P4V77/DiplomaThesis/LaTeX/kapitola2/figures/block_diagram.pdf

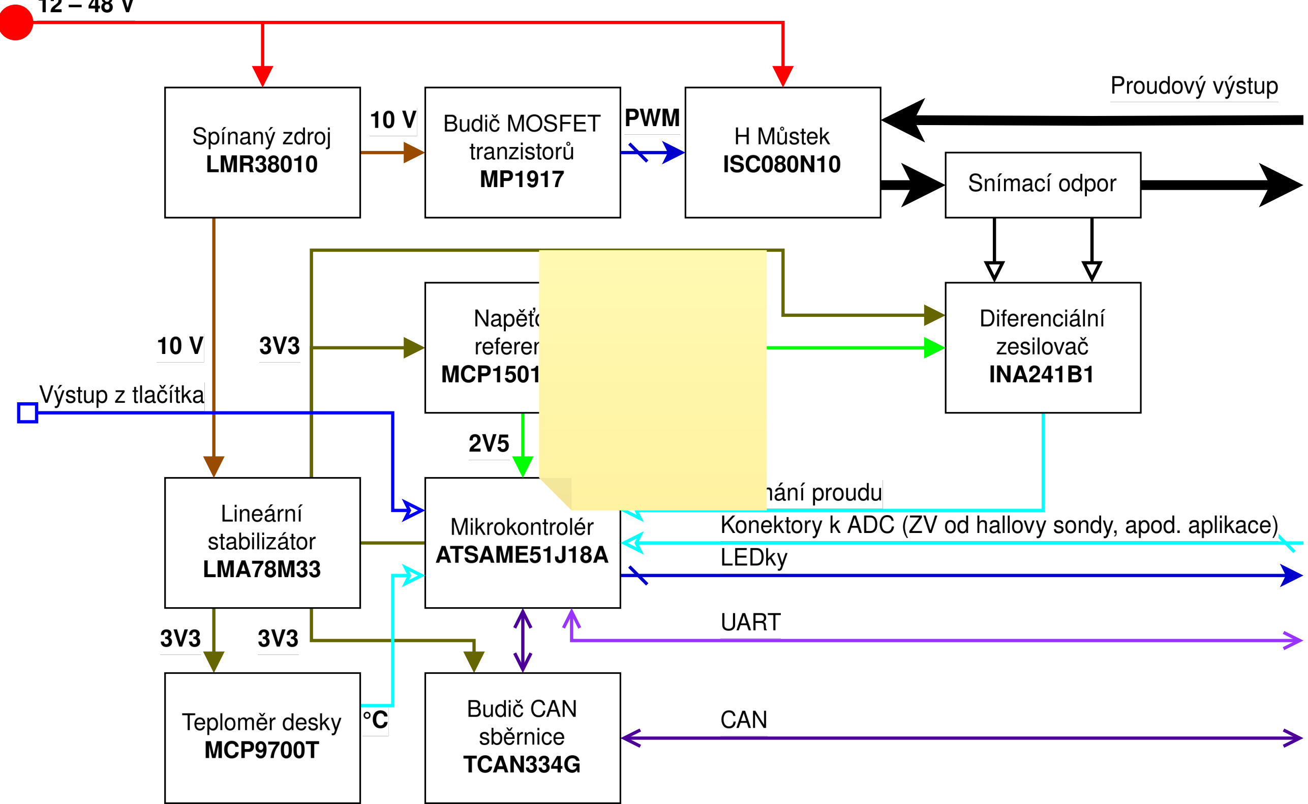
[picture p20: figure]
