P4V77/DiplomaThesis/LaTeX/kapitola2/figures/can_connector.pdf

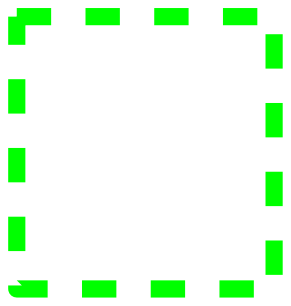
[picture p21: page 1]
