P4V77/DiplomaThesis/LaTeX/kapitola3/figures/boxes_back.pdf

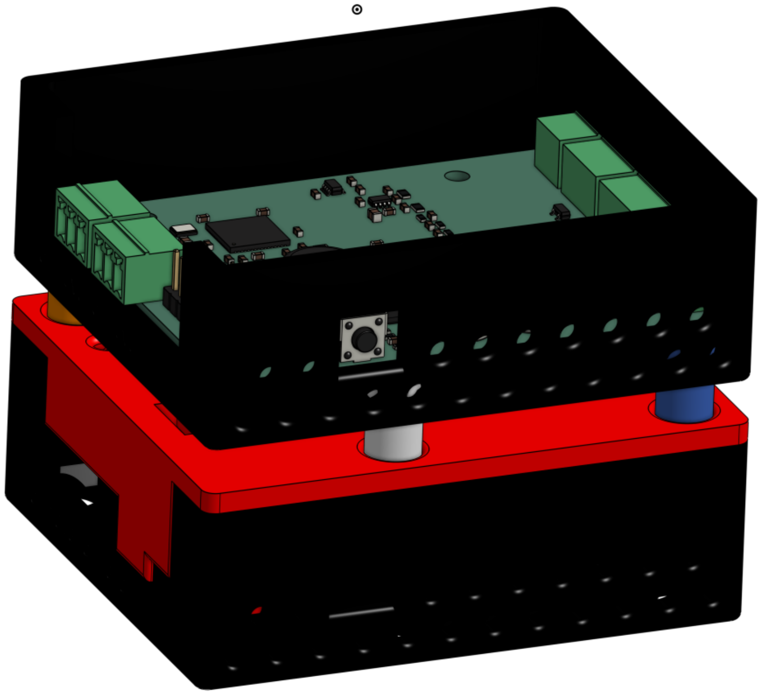
[picture p22: page 1]
