P4V77/DiplomaThesis/LaTeX/kapitola3/figures/boxes_front.pdf

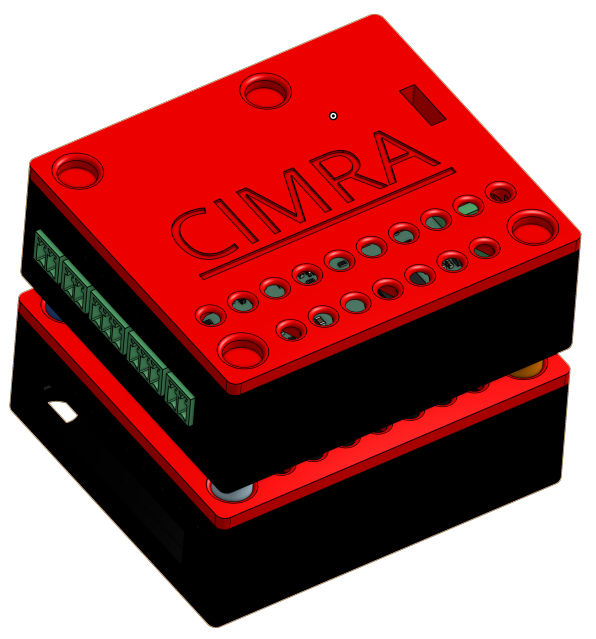
[picture p23: page 1]
