P4V77/DiplomaThesis/LaTeX/kapitola3/figures/pap_holder.pdf

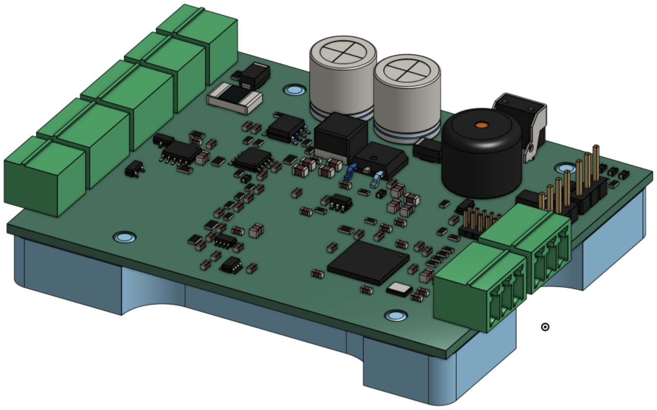
[picture p24: page 1]
