P4V77/DiplomaThesis/LaTeX/kapitola4/figures/flowchart_regulator_current.pdf

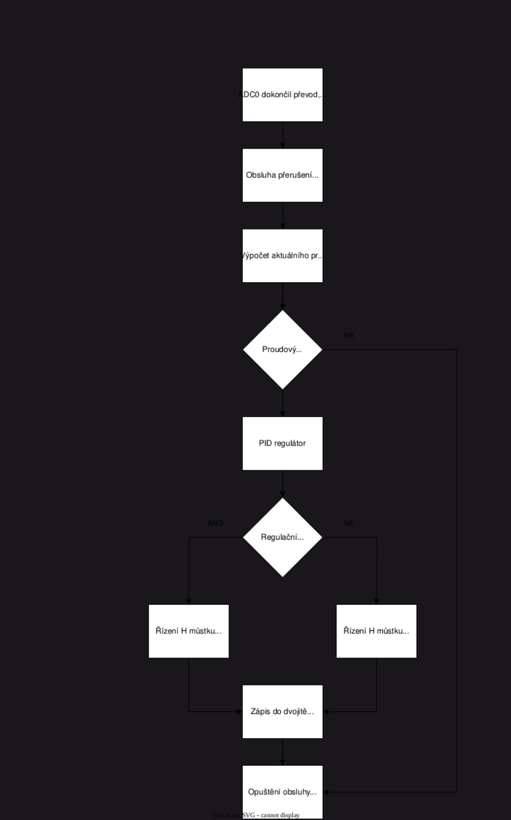
[picture p25: page 1]
