P4V77/DiplomaThesis/HW/Loga/cimra.png

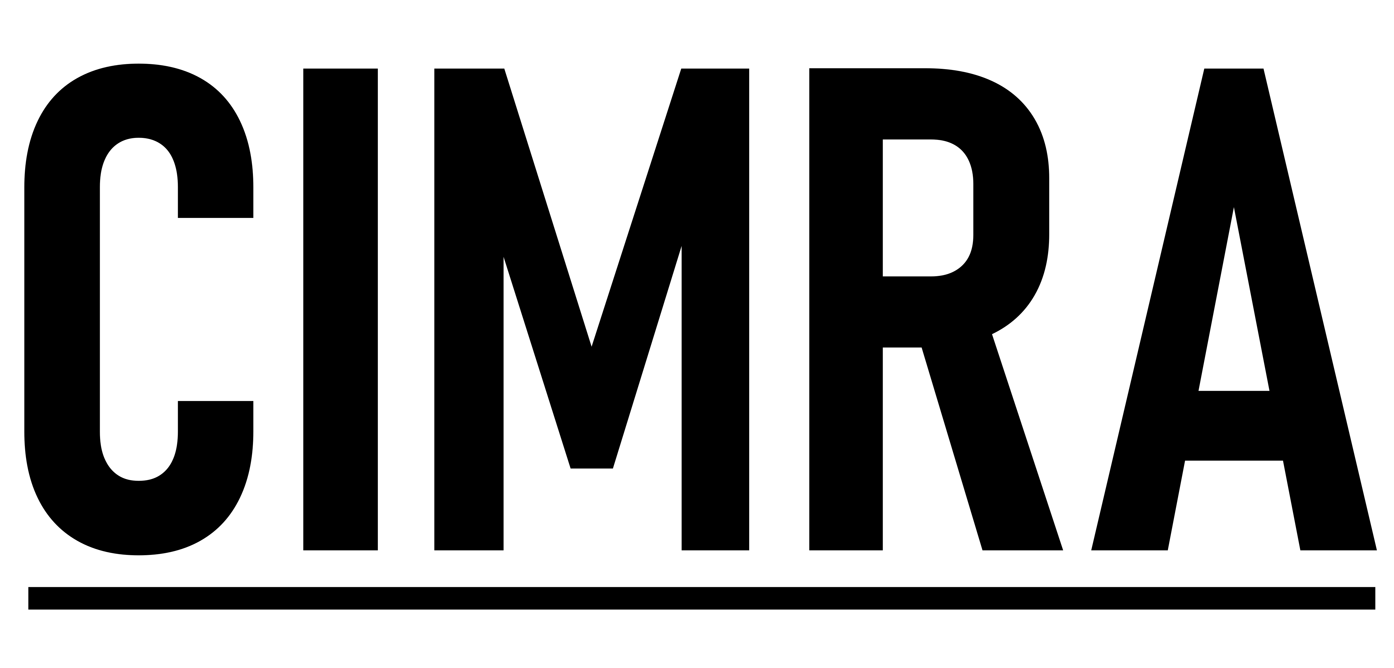
HW/Loga/cimra.png
