P4V77/DiplomaThesis/HW/Loga/ZCU.png

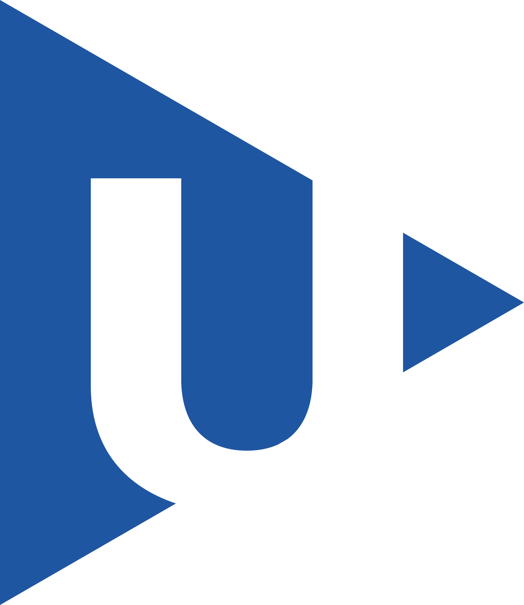
HW/Loga/ZCU.png
