P4V77/DiplomaThesis/LaTeX/kapitola5/Figures/Analyza_THD.png

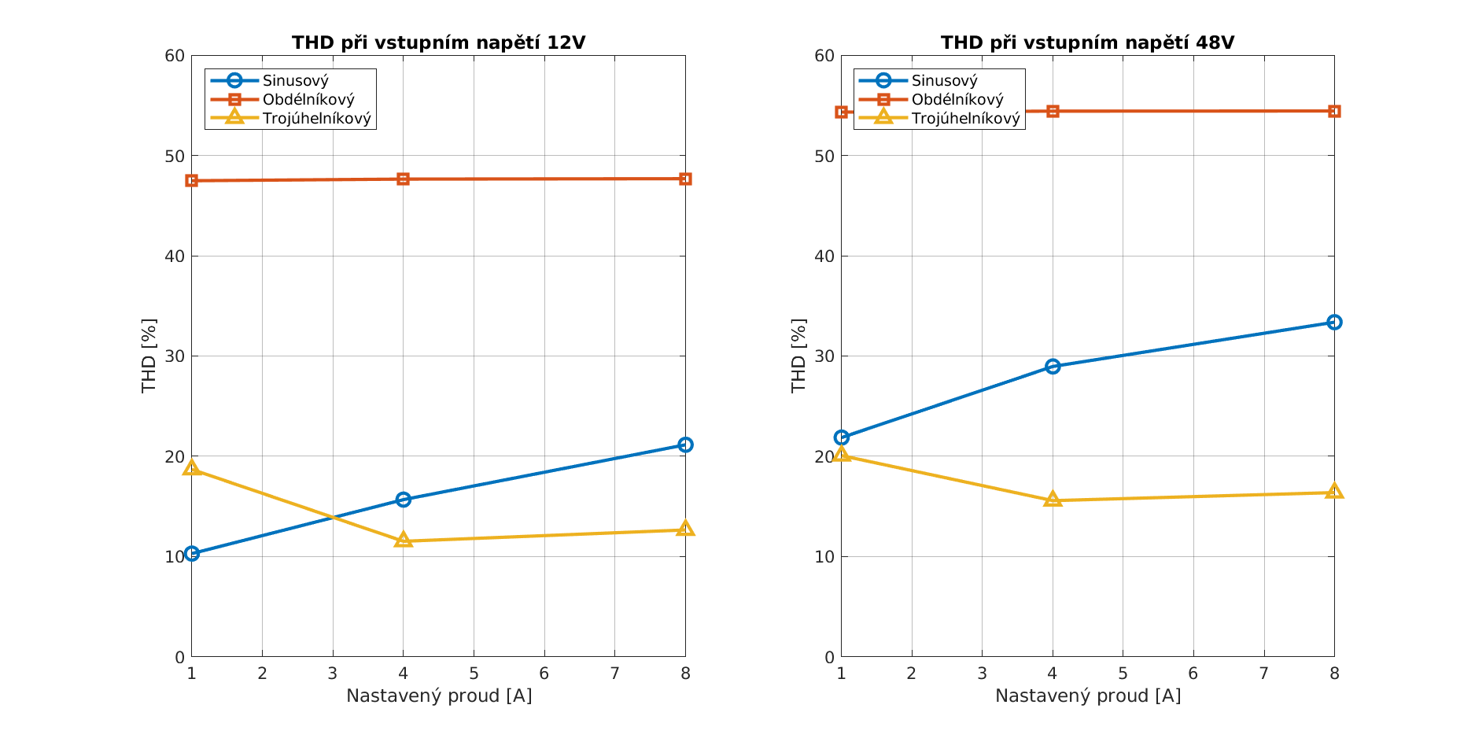
LaTeX/kapitola5/Figures/Analyza_THD.png
