P4V77/DiplomaThesis/LaTeX/kapitola5/Figures/Analyza_zakladni_harmonicke.png

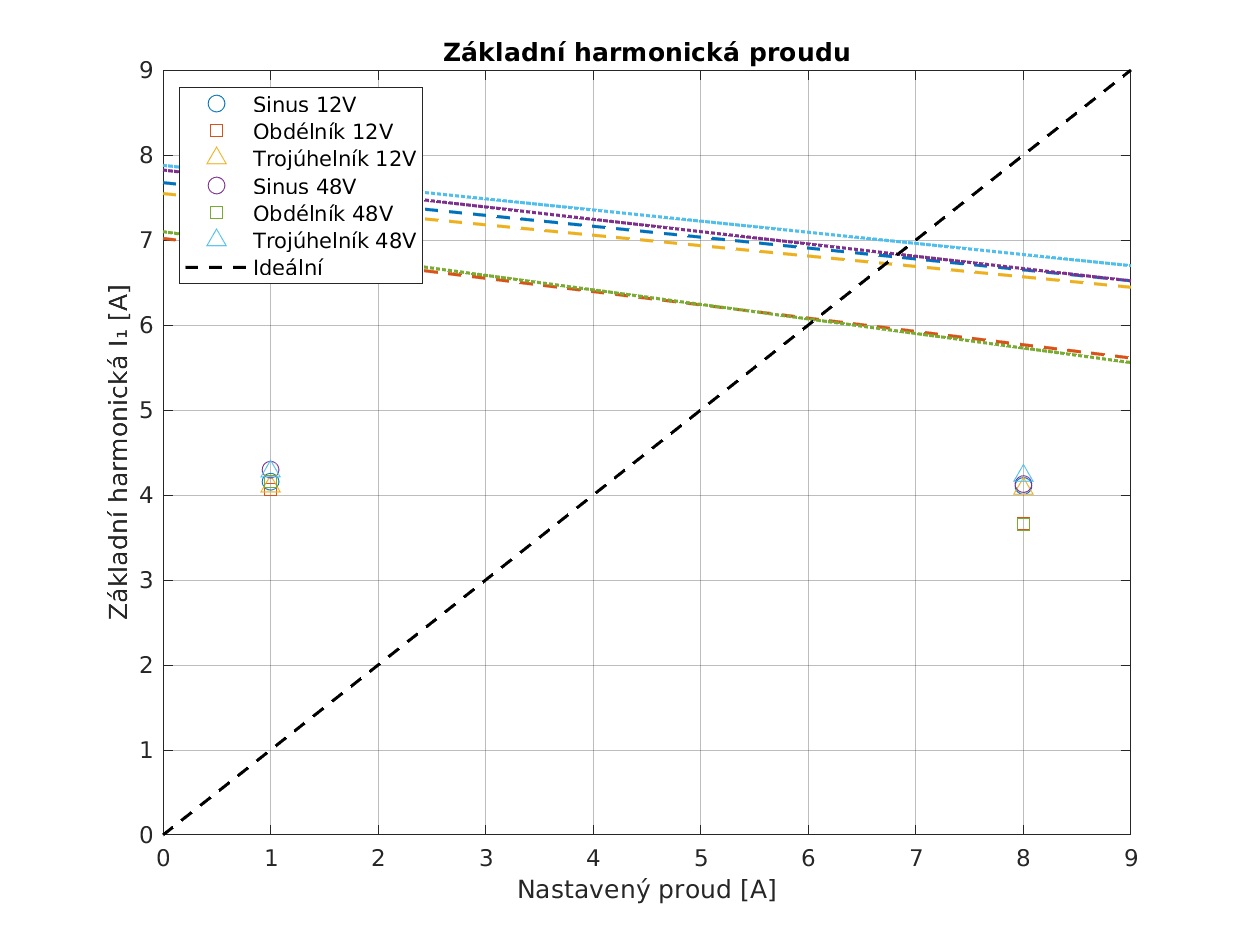
LaTeX/kapitola5/Figures/Analyza_zakladni_harmonicke.png
