P4V77/DiplomaThesis/LaTeX/kapitola5/Figures/Analyza_zakladni_harmonicke_smooth.png

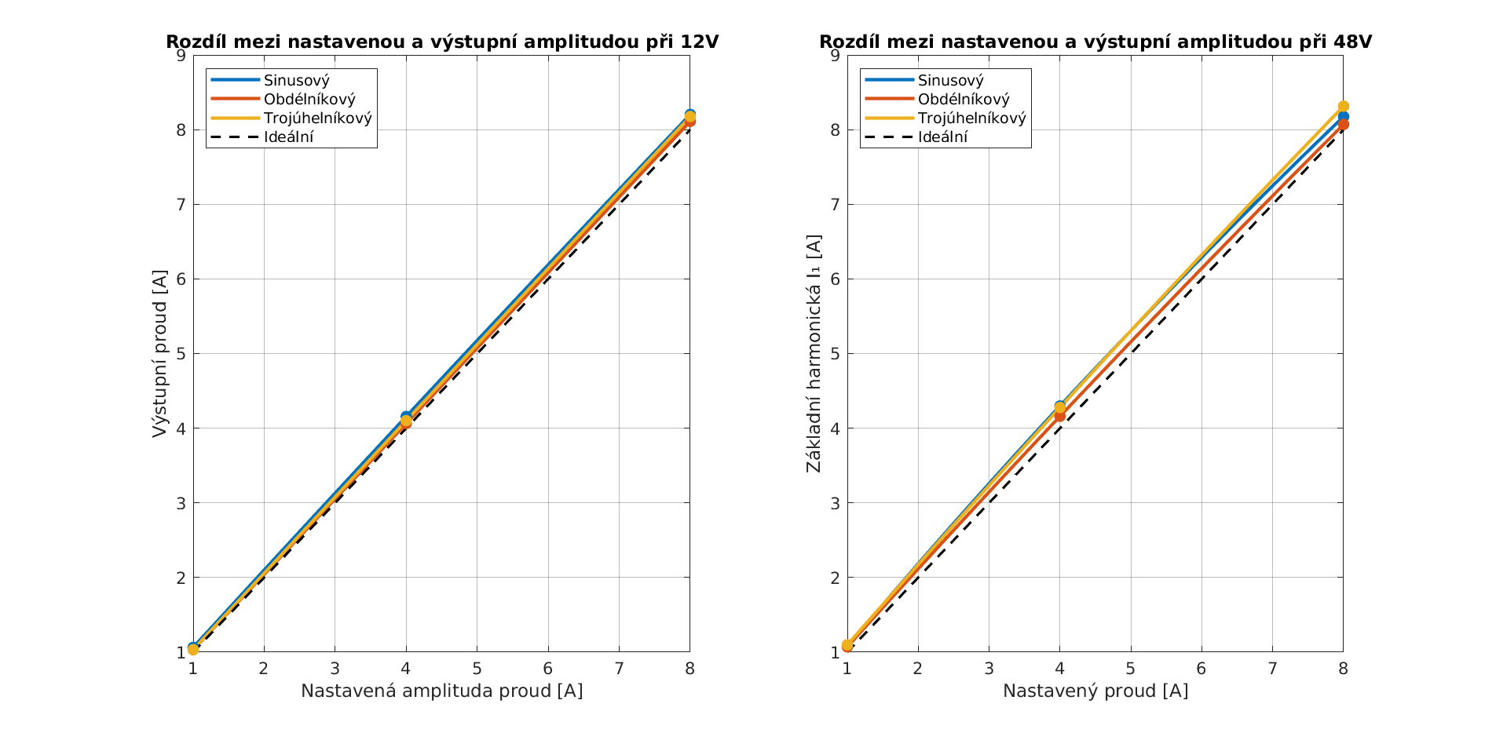
LaTeX/kapitola5/Figures/Analyza_zakladni_harmonicke_smooth.png
