P4V77/DiplomaThesis/LaTeX/kapitola5/Figures/DC_IRMS.png

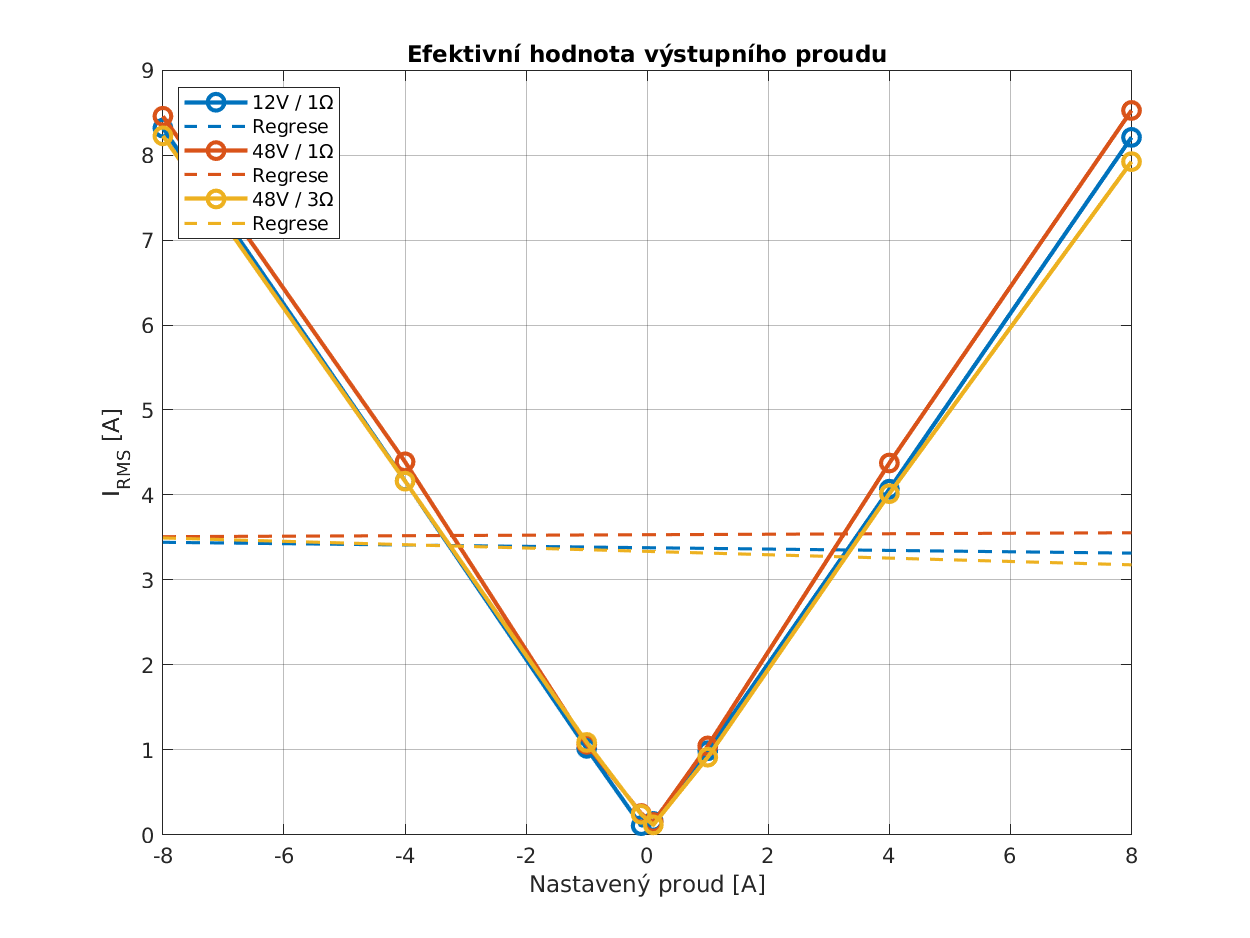
LaTeX/kapitola5/Figures/DC_IRMS.png
