P4V77/DiplomaThesis/LaTeX/kapitola5/Figures/DC_ucinnost_31V.png

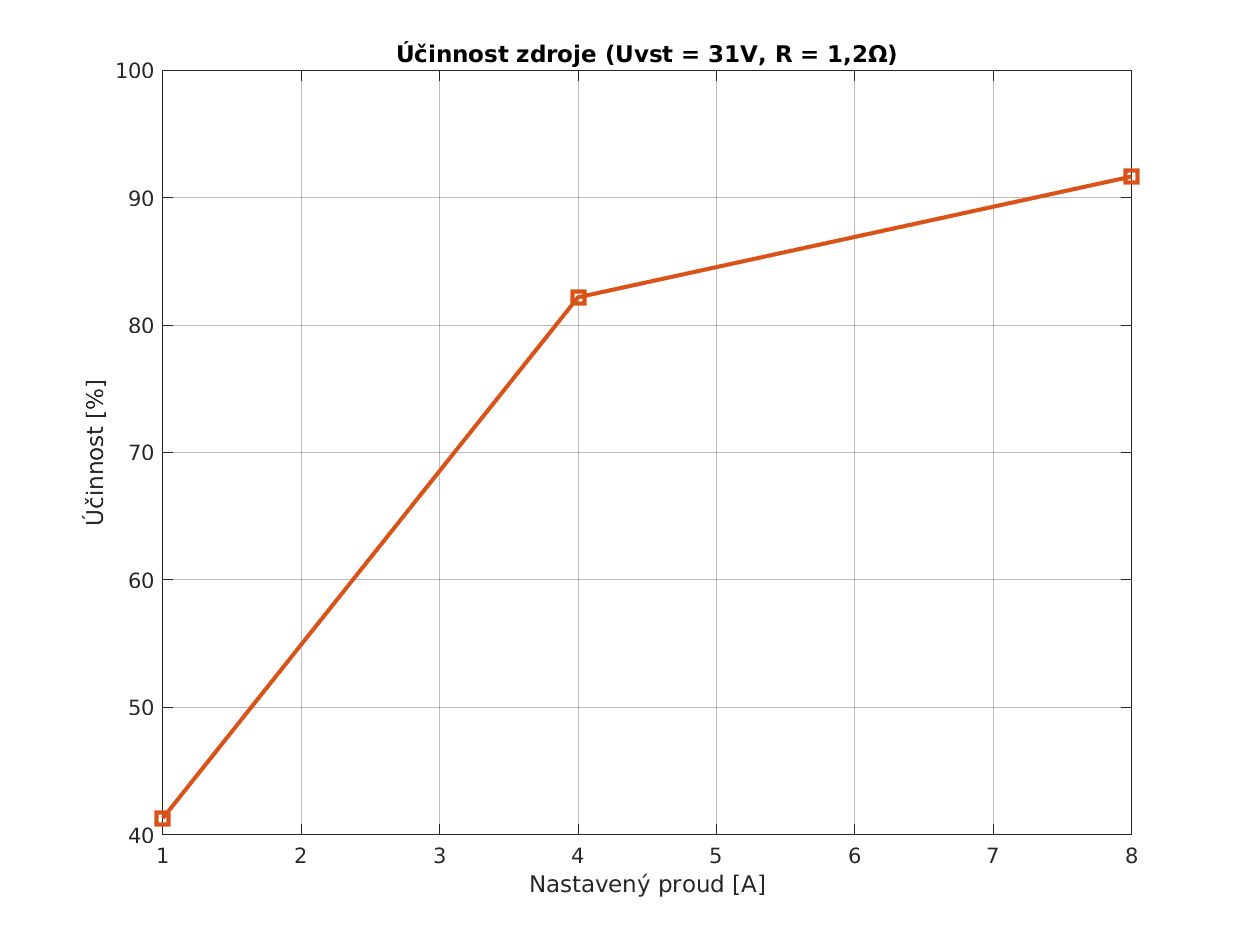
LaTeX/kapitola5/Figures/DC_ucinnost_31V.png
