P4V77/DiplomaThesis/LaTeX/kapitola5/Figures/DC_zvlneni_pp.png

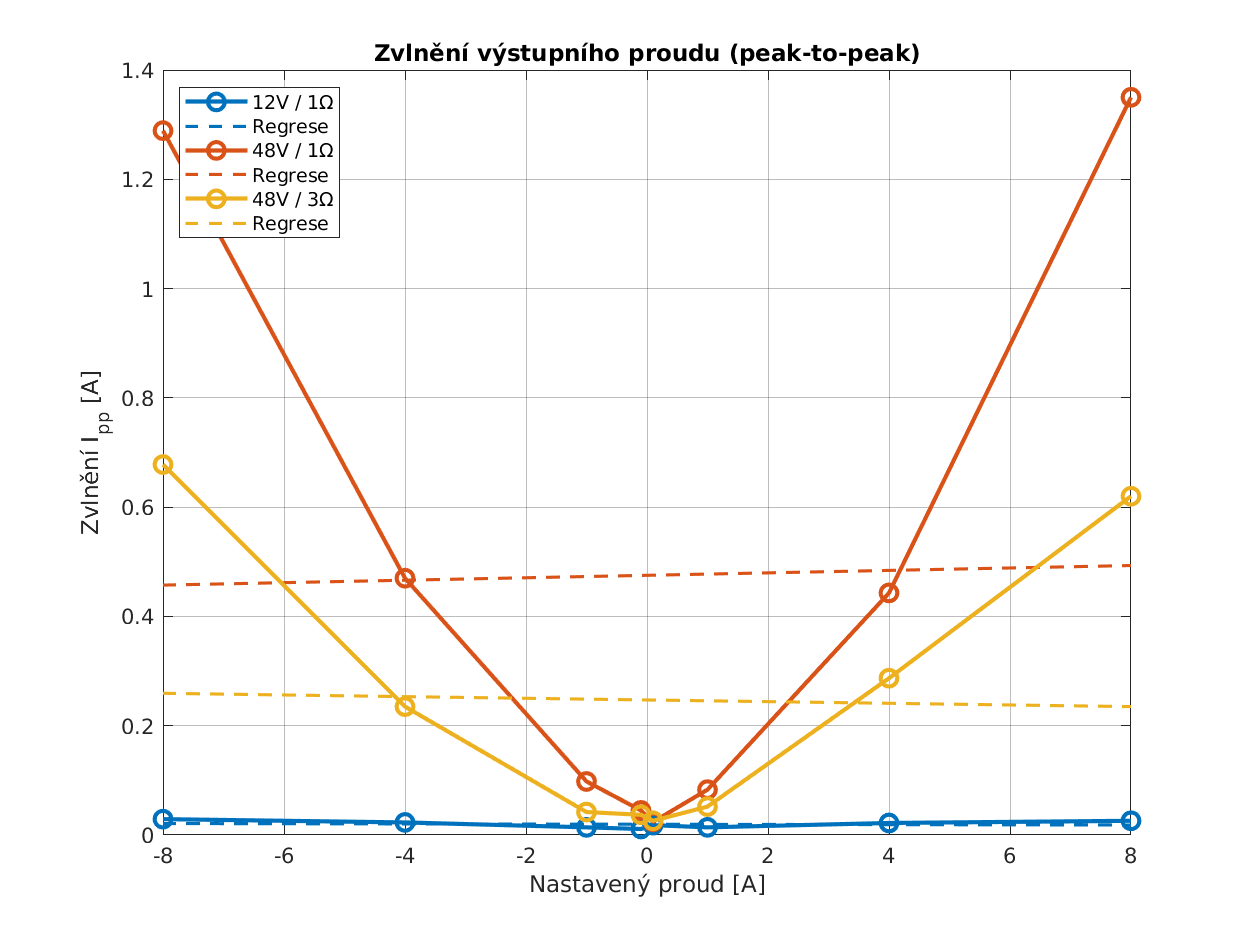
LaTeX/kapitola5/Figures/DC_zvlneni_pp.png
