P4V77/DiplomaThesis/LaTeX/kapitola5/Figures/Fundamental_Current.png

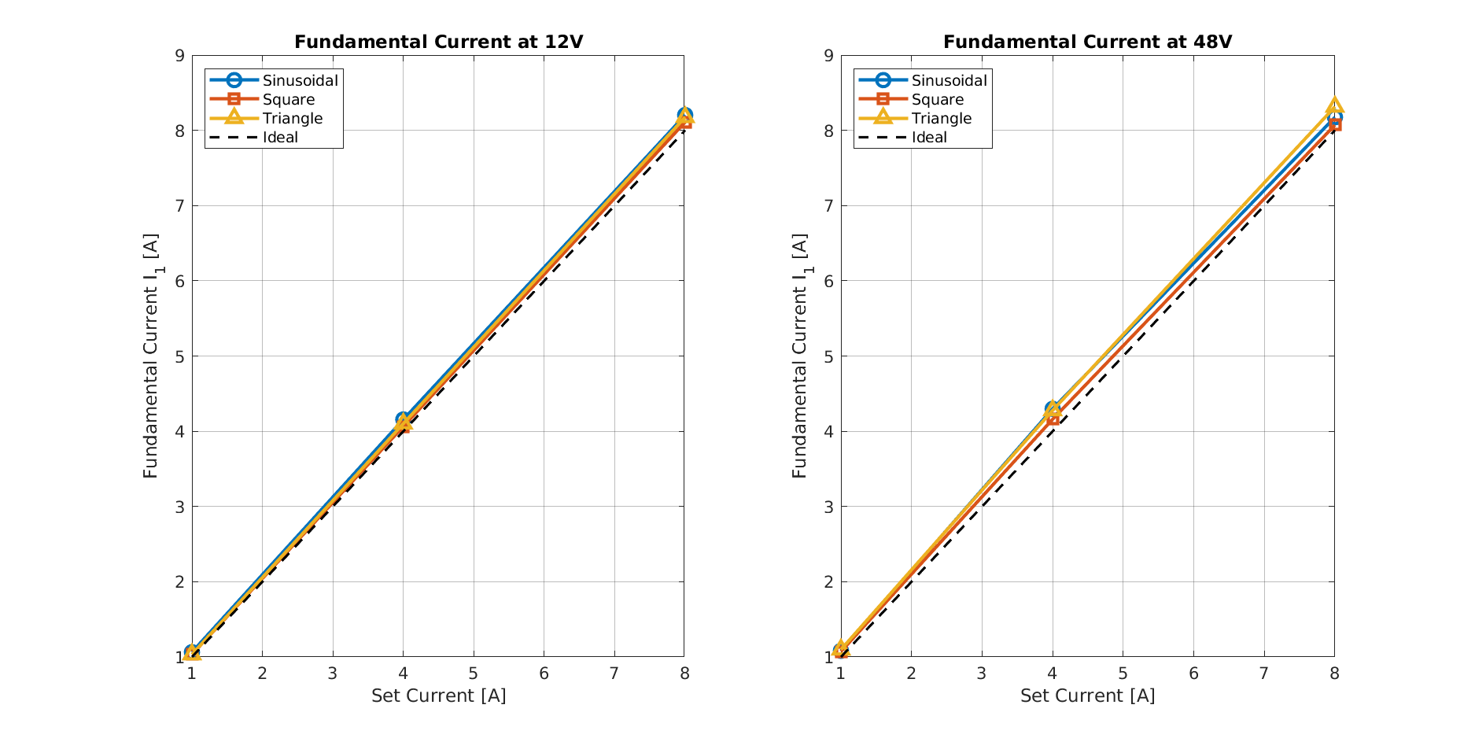
LaTeX/kapitola5/Figures/Fundamental_Current.png
