P4V77/DiplomaThesis/LaTeX/kapitola5/Figures/Graf4_Zatezova_char_napeti.png

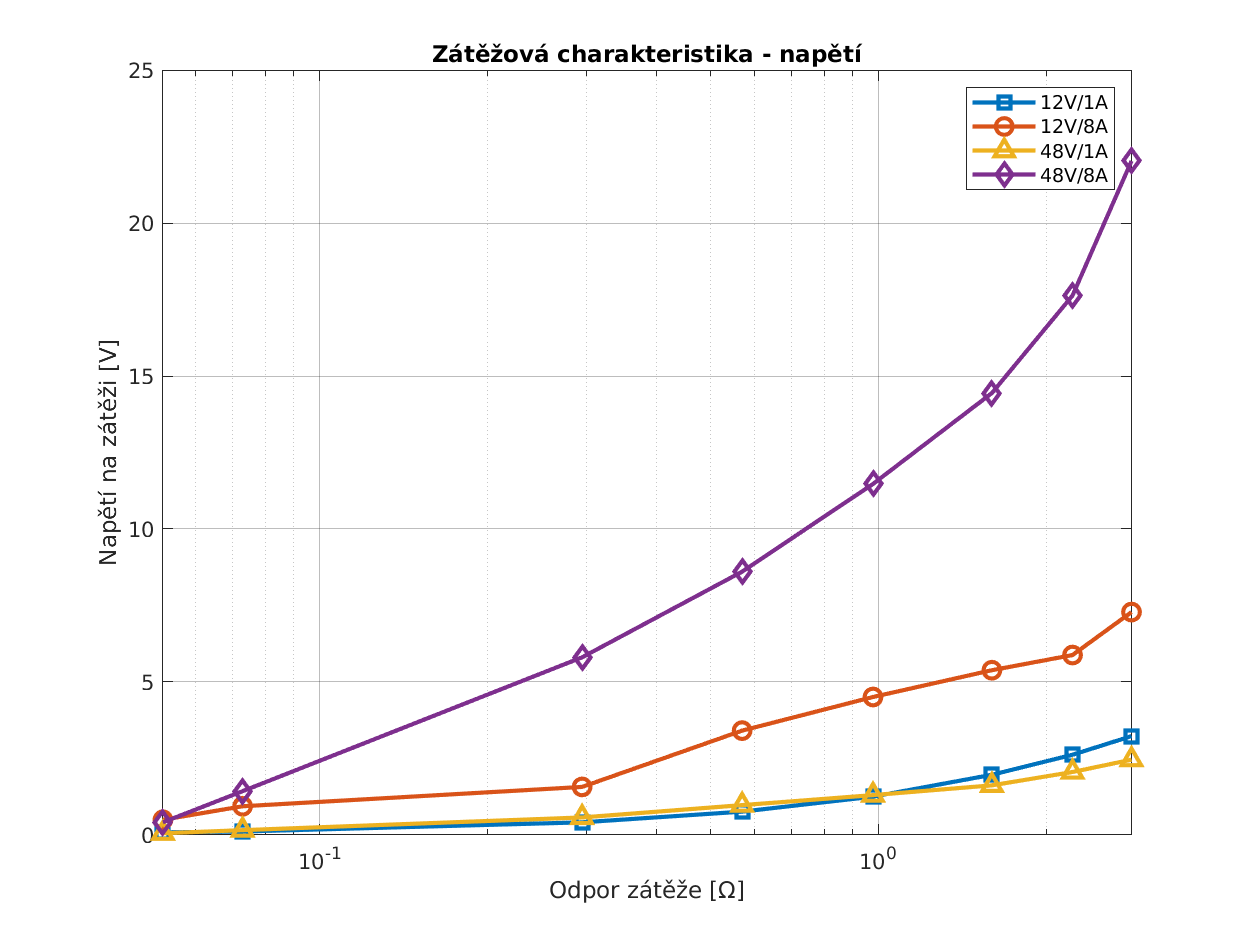
LaTeX/kapitola5/Figures/Graf4_Zatezova_char_napeti.png
