P4V77/DiplomaThesis/LaTeX/kapitola5/Figures/THD_kombinovane.png

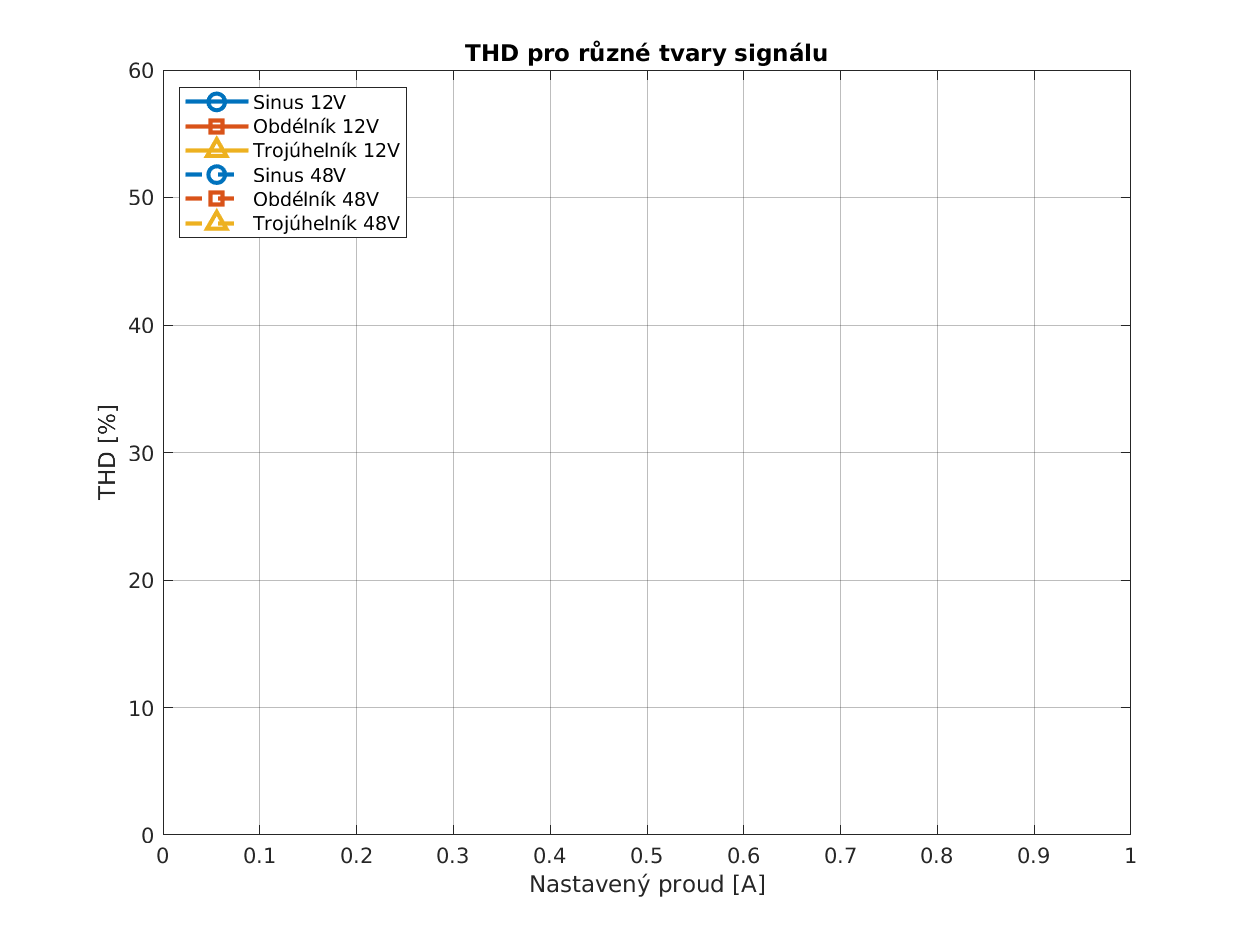
LaTeX/kapitola5/Figures/THD_kombinovane.png
