P4V77/DiplomaThesis/LaTeX/kapitola5/Figures/Zakladni_harmonicka_kombinovane.png

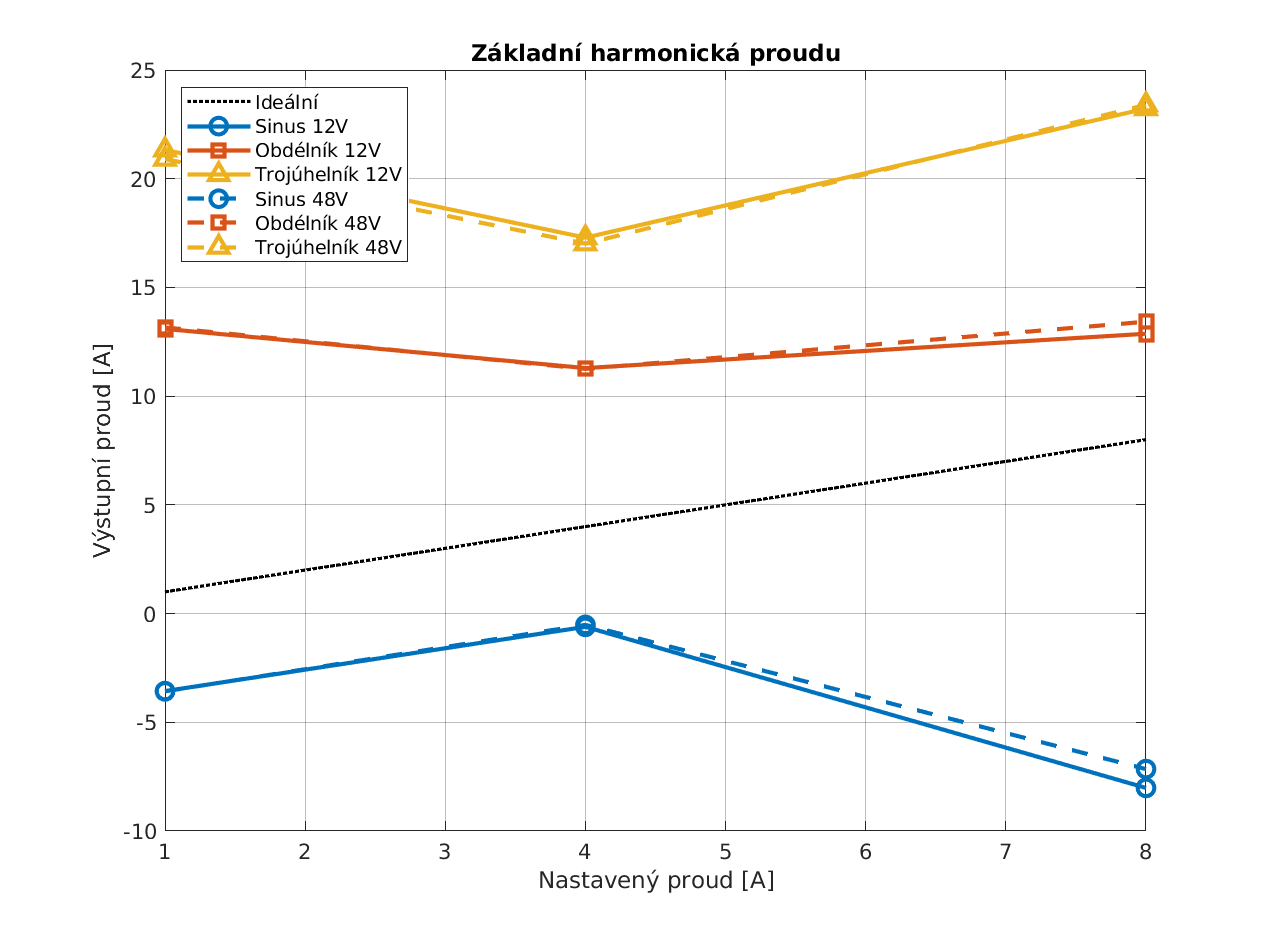
LaTeX/kapitola5/Figures/Zakladni_harmonicka_kombinovane.png
