P4V77/DiplomaThesis/LaTeX/kapitola7/Figures/Screenshot from 2025-05-09 12-28-37.png

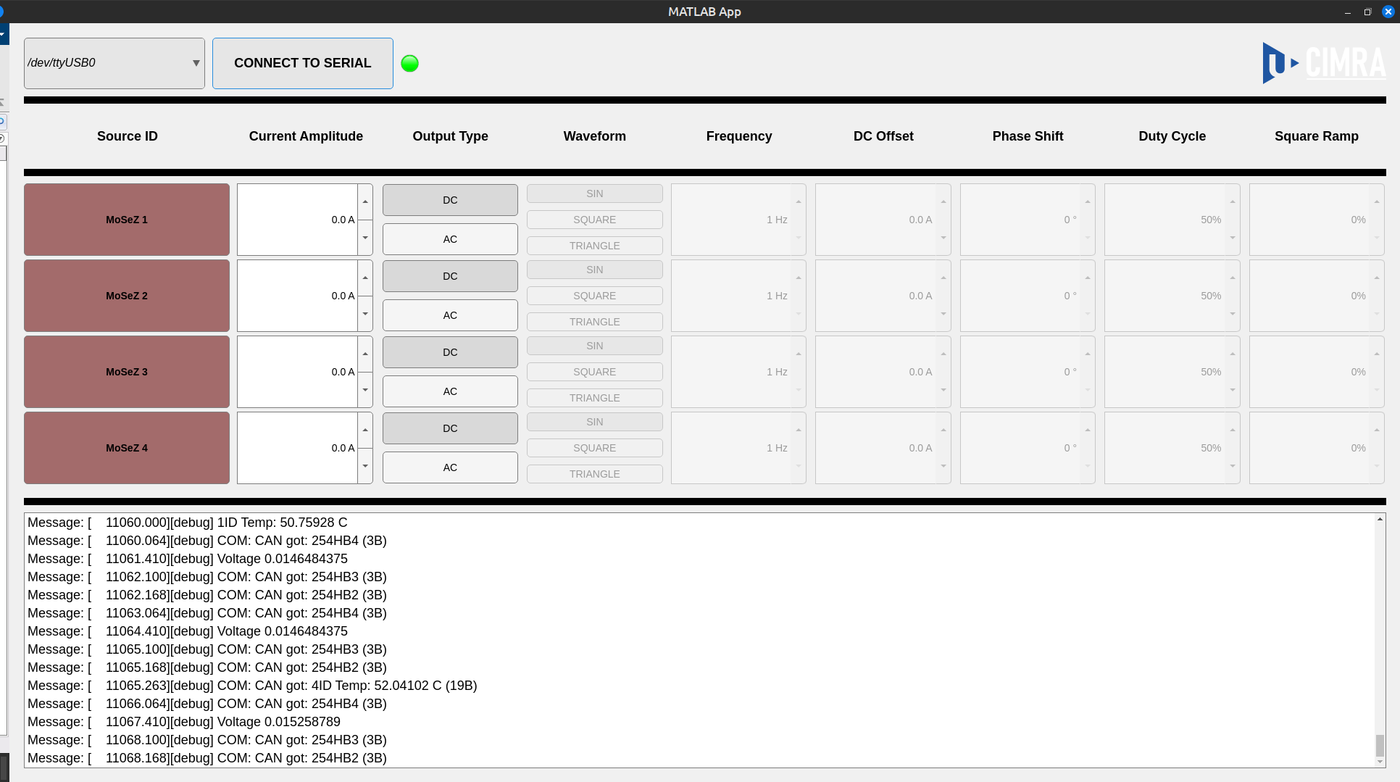
LaTeX/kapitola7/Figures/Screenshot from 2025-05-09 12-28-37.png
