P4V77/DiplomaThesis/LaTeX/kapitola7/Figures/Screenshot from 2025-05-09 12-29-39.png

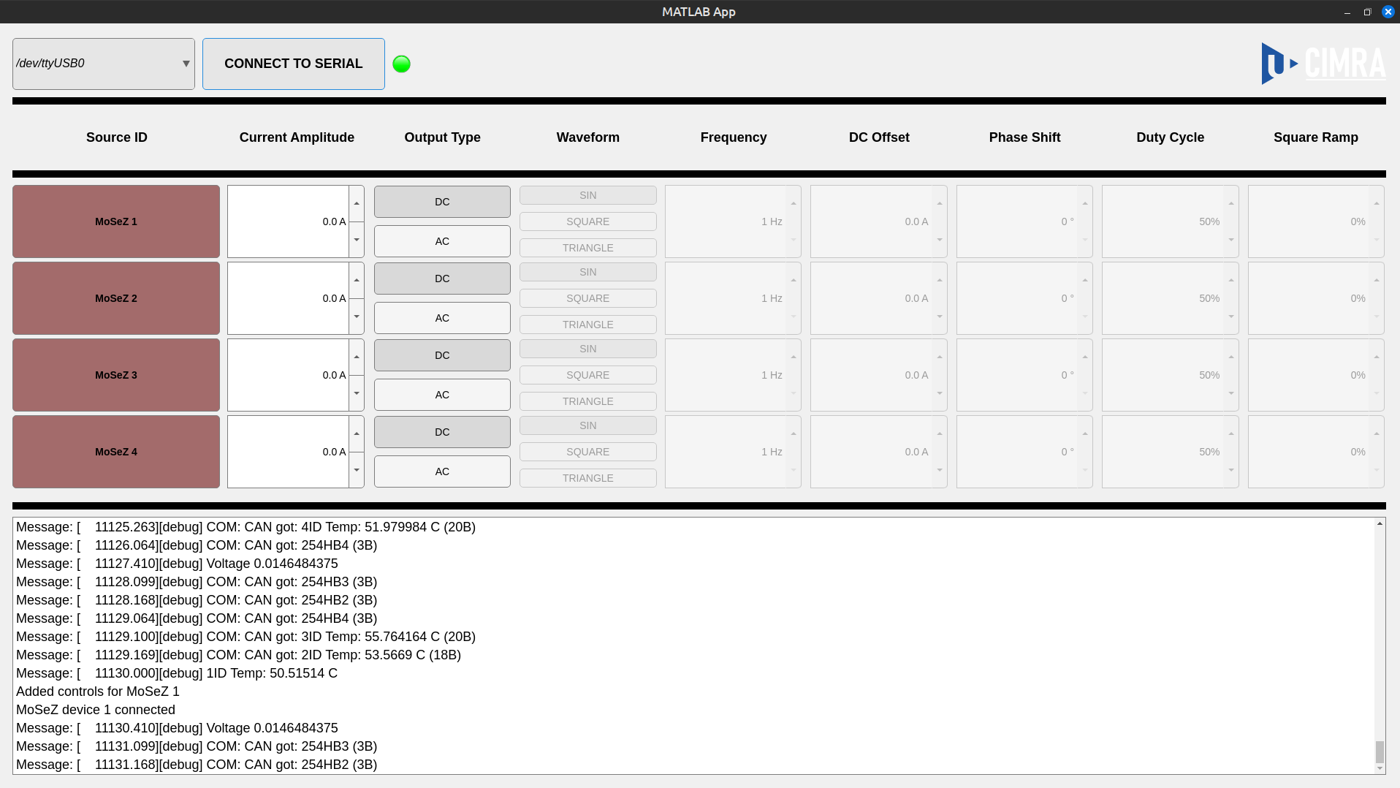
LaTeX/kapitola7/Figures/Screenshot from 2025-05-09 12-29-39.png
