P4V77/DiplomaThesis/Meassurements/Mereni/output_plot.png

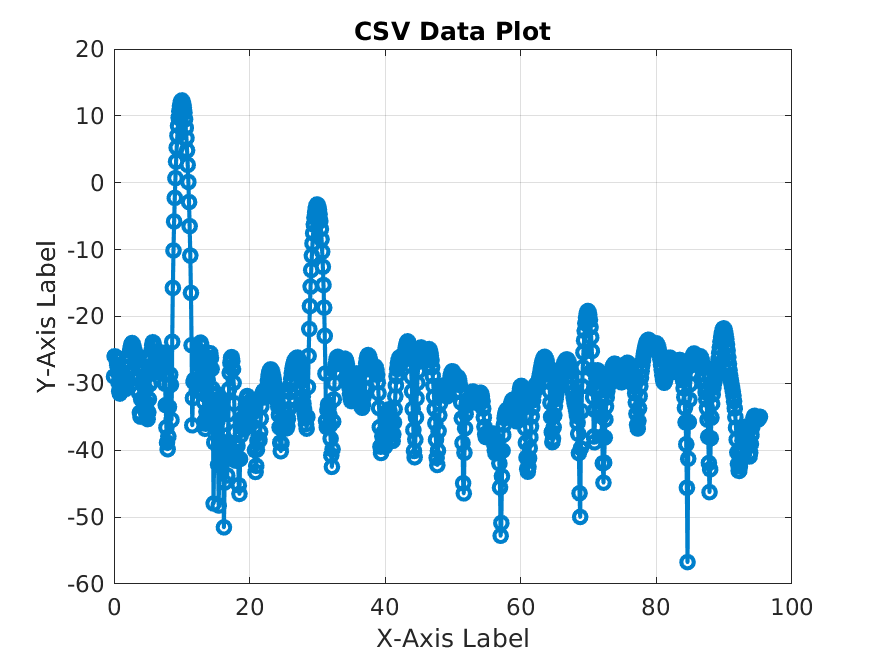
Meassurements/Mereni/output_plot.png
