P4V77/DiplomaThesis/Meassurements/Mereni/output_plot_1000.png

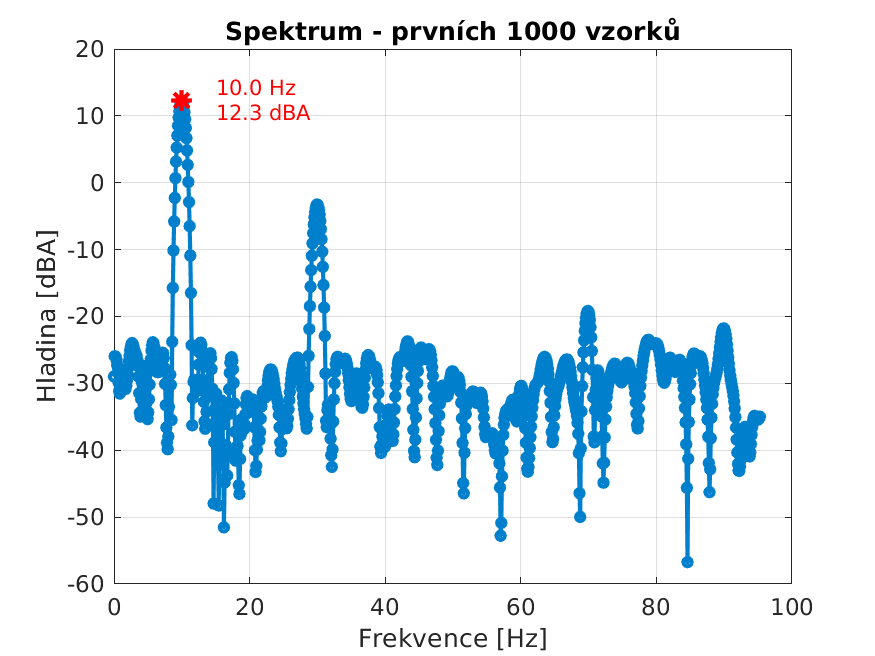
Meassurements/Mereni/output_plot_1000.png
