P4V77/DiplomaThesis/Meassurements/Skripty/Current_Efficiency.png

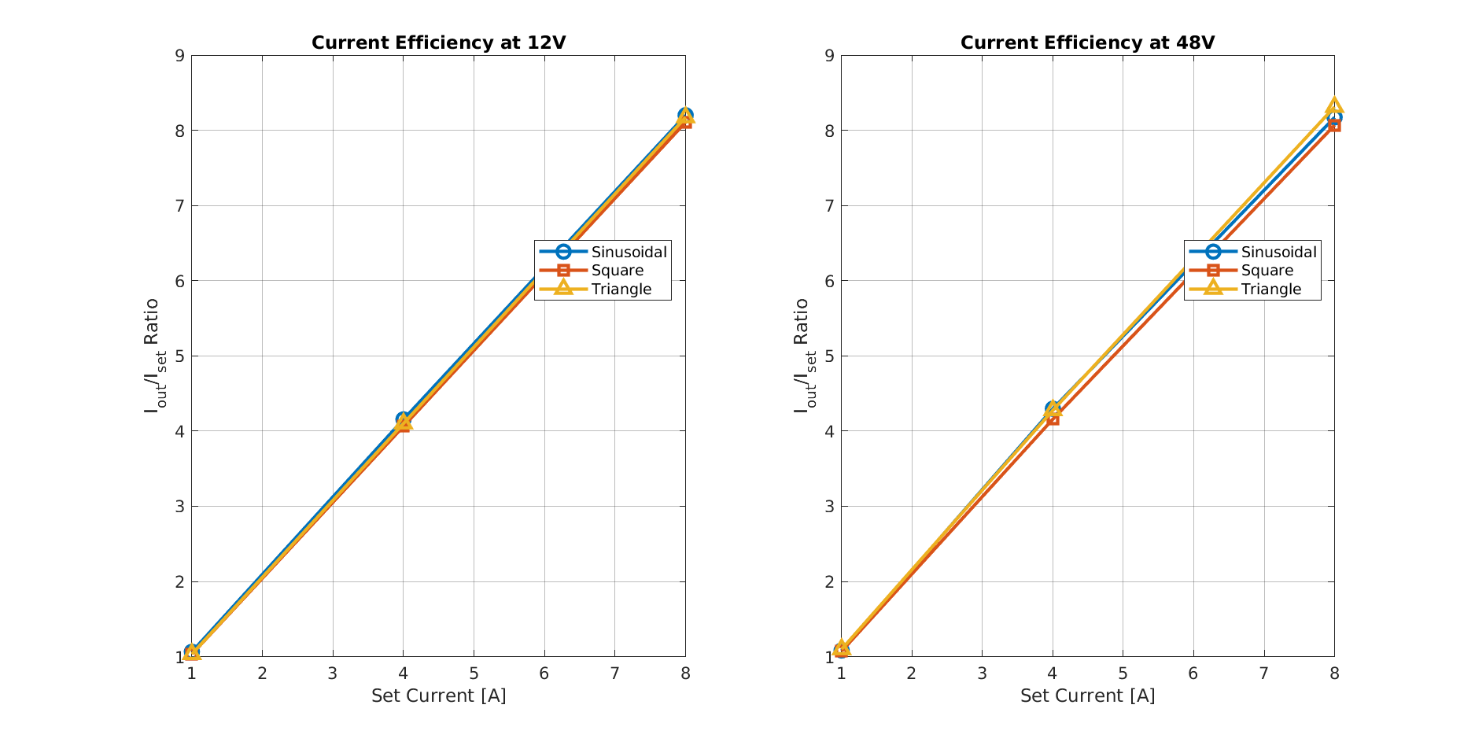
Meassurements/Skripty/Current_Efficiency.png
