P4V77/DiplomaThesis/Meassurements/Termokamera/SNAP0004.jpg

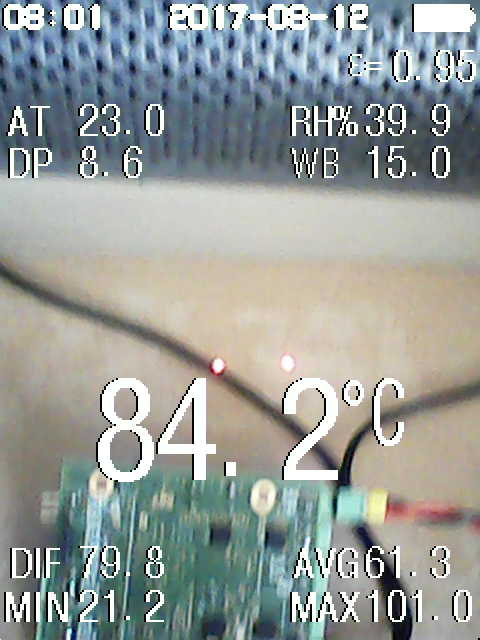
Meassurements/Termokamera/SNAP0004.jpg
