P4V77/DiplomaThesis/Meassurements/Termokamera/SNAP0005.jpg

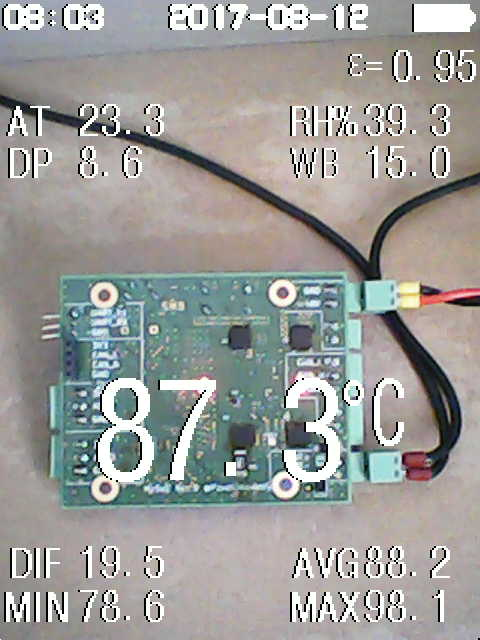
Meassurements/Termokamera/SNAP0005.jpg
