P4V77/DiplomaThesis/Meassurements/Termokamera/SNAP0006.jpg

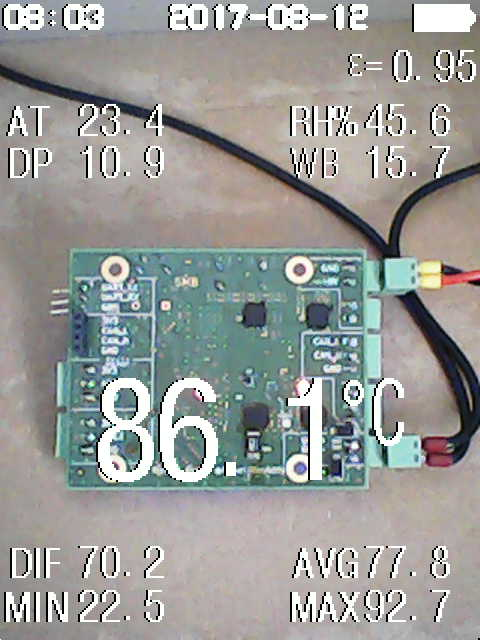
Meassurements/Termokamera/SNAP0006.jpg
