P4V77/DiplomaThesis/Meassurements/Termokamera/SNAP0007.jpg

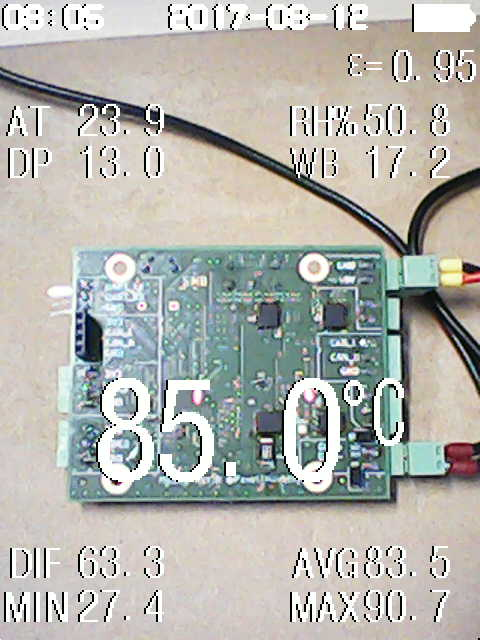
Meassurements/Termokamera/SNAP0007.jpg
