P4V77/DiplomaThesis/Meassurements/Termokamera/SNAP0008.jpg

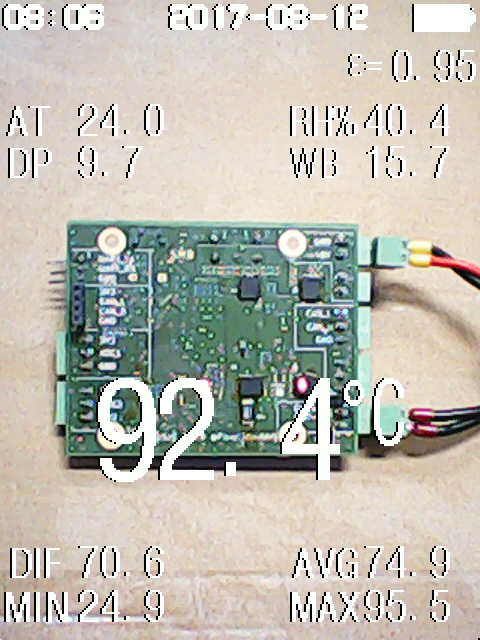
Meassurements/Termokamera/SNAP0008.jpg
