P4V77/DiplomaThesis/Meassurements/Termokamera/SNAP0009.jpg

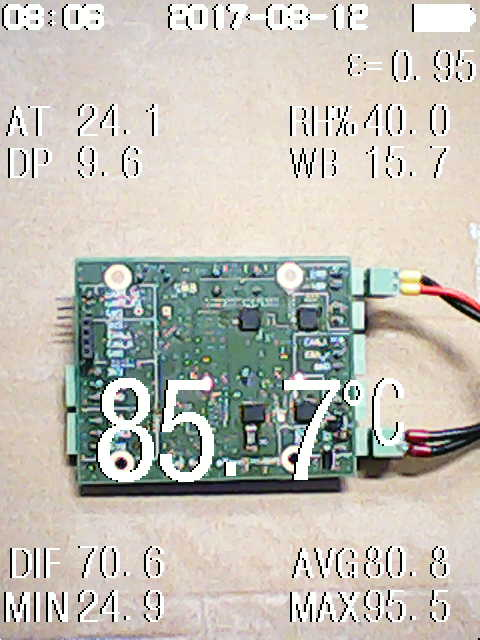
Meassurements/Termokamera/SNAP0009.jpg
