P4V77/DiplomaThesis/Meassurements/Termokamera/SNAP0010.jpg

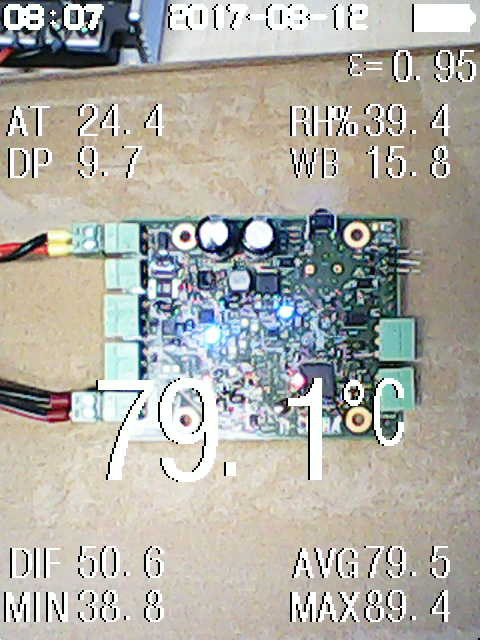
Meassurements/Termokamera/SNAP0010.jpg
