P4V77/DiplomaThesis/SW(MattlabApp)/cimra.png

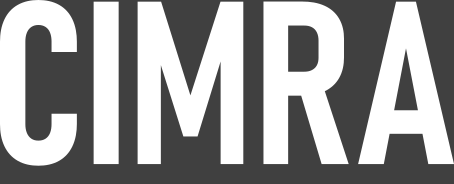
SW(MattlabApp)/cimra.png
