P4V77/DiplomaThesis/LaTeX/prilohy/prilohaA/schema.pdf

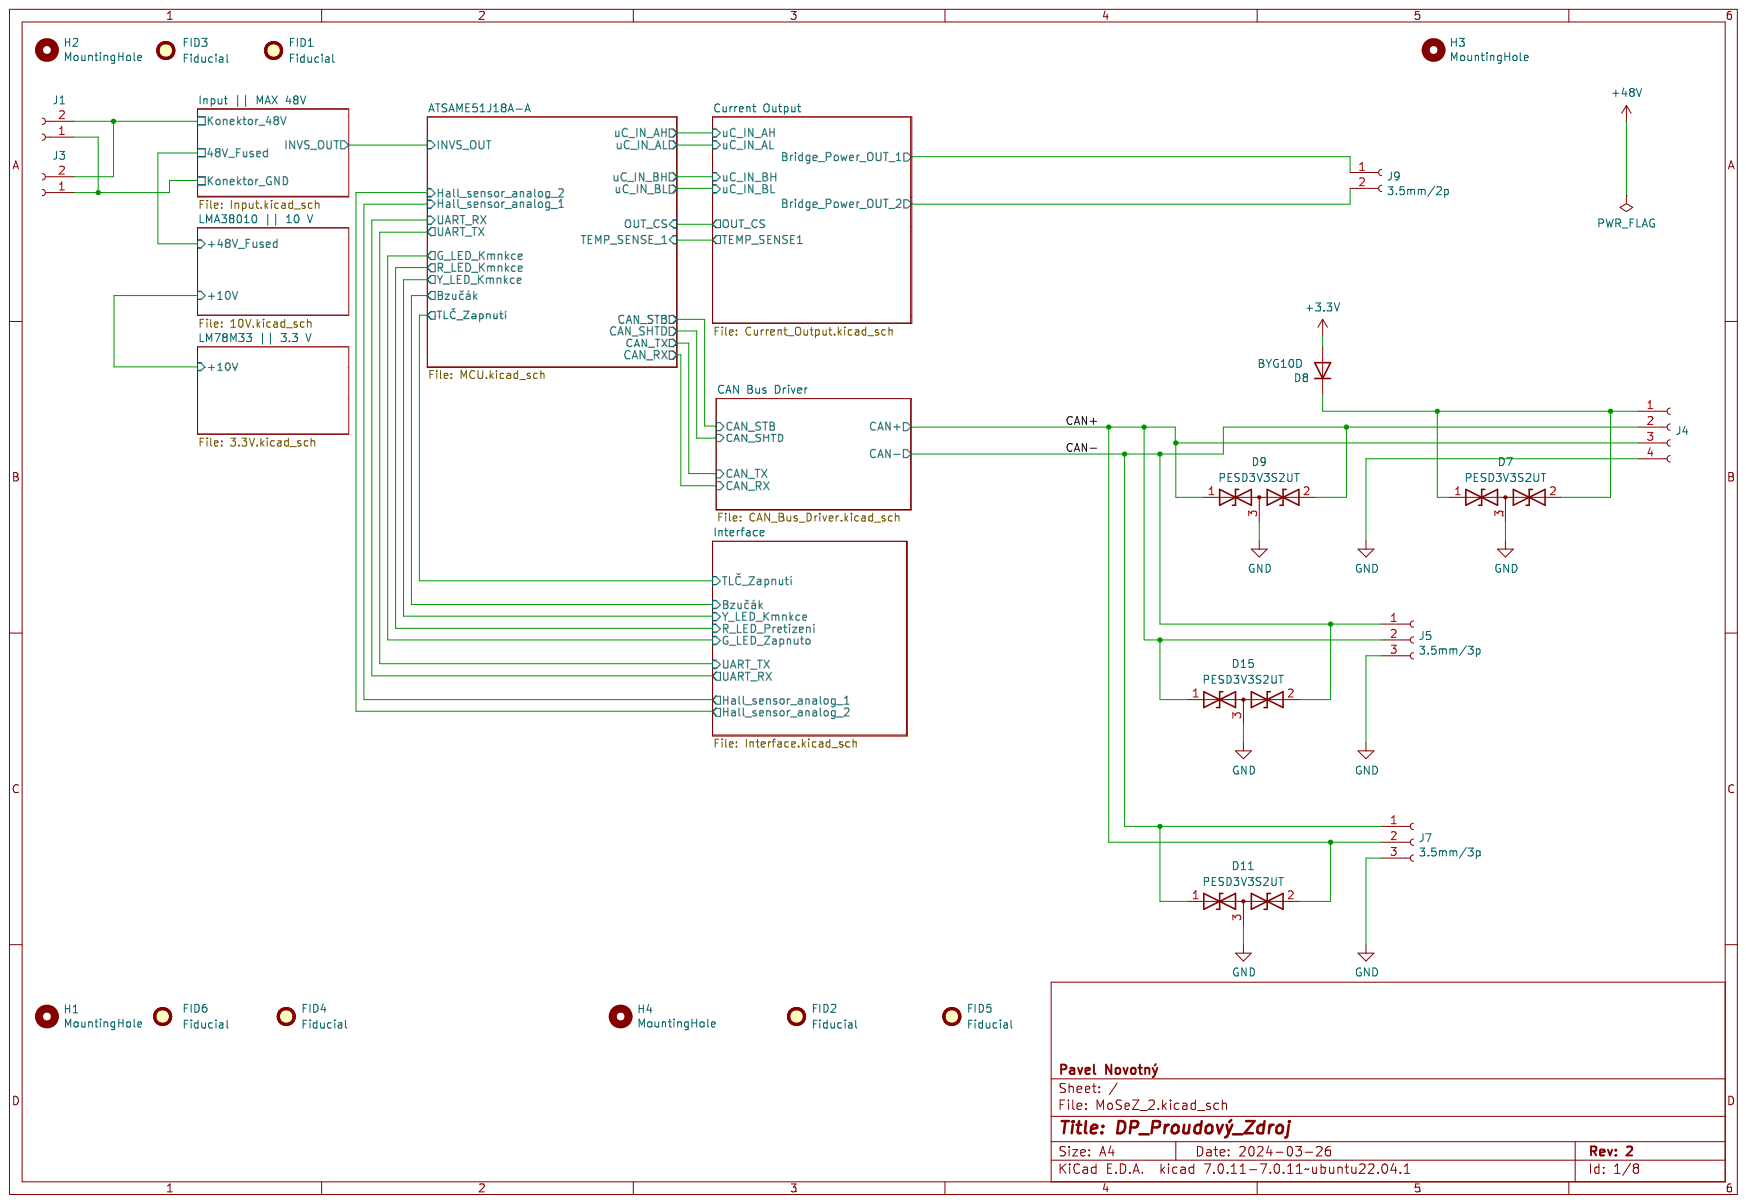
[picture p65: page 1]

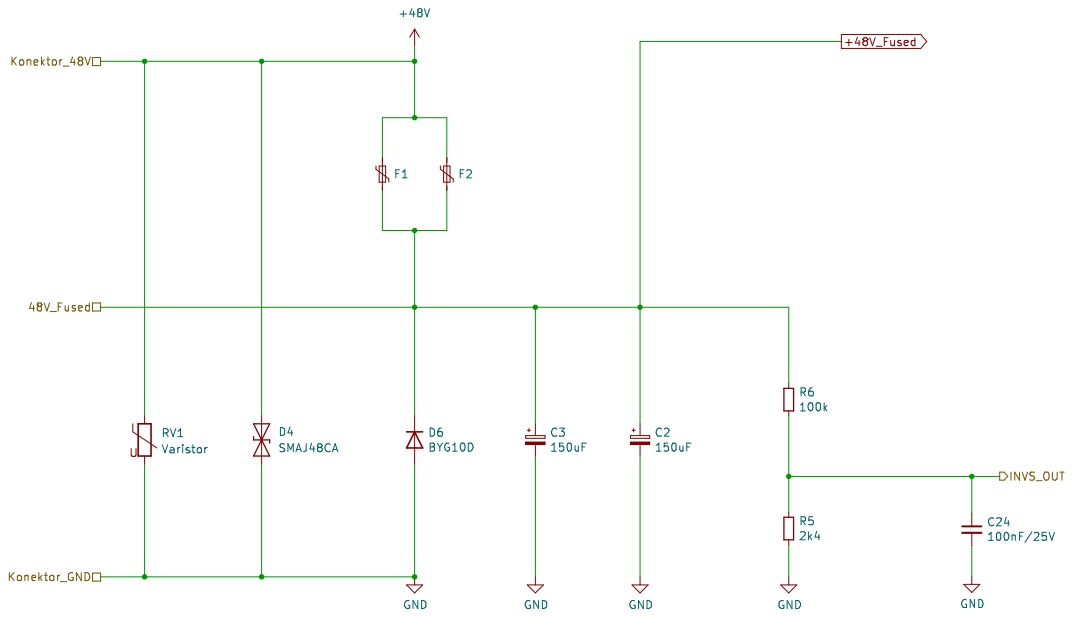
[picture p66: page 2]

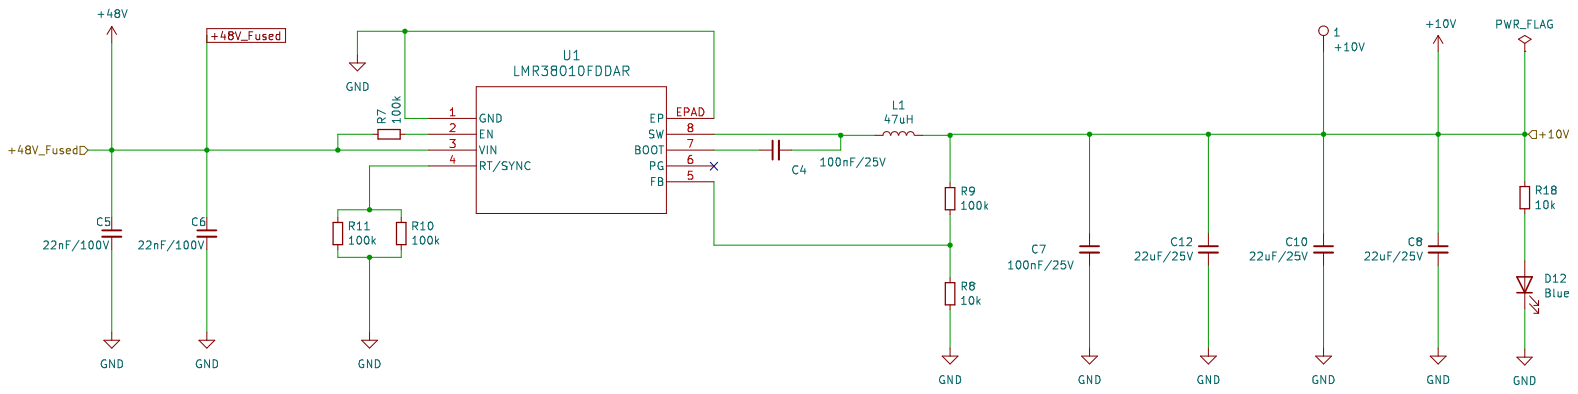
[picture p67: page 3]

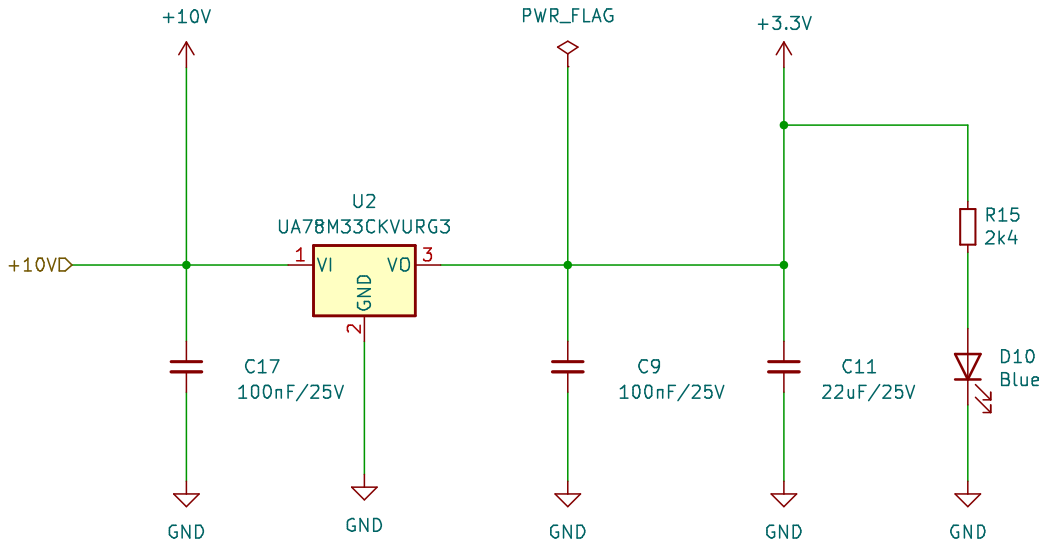
[picture p68: page 4]

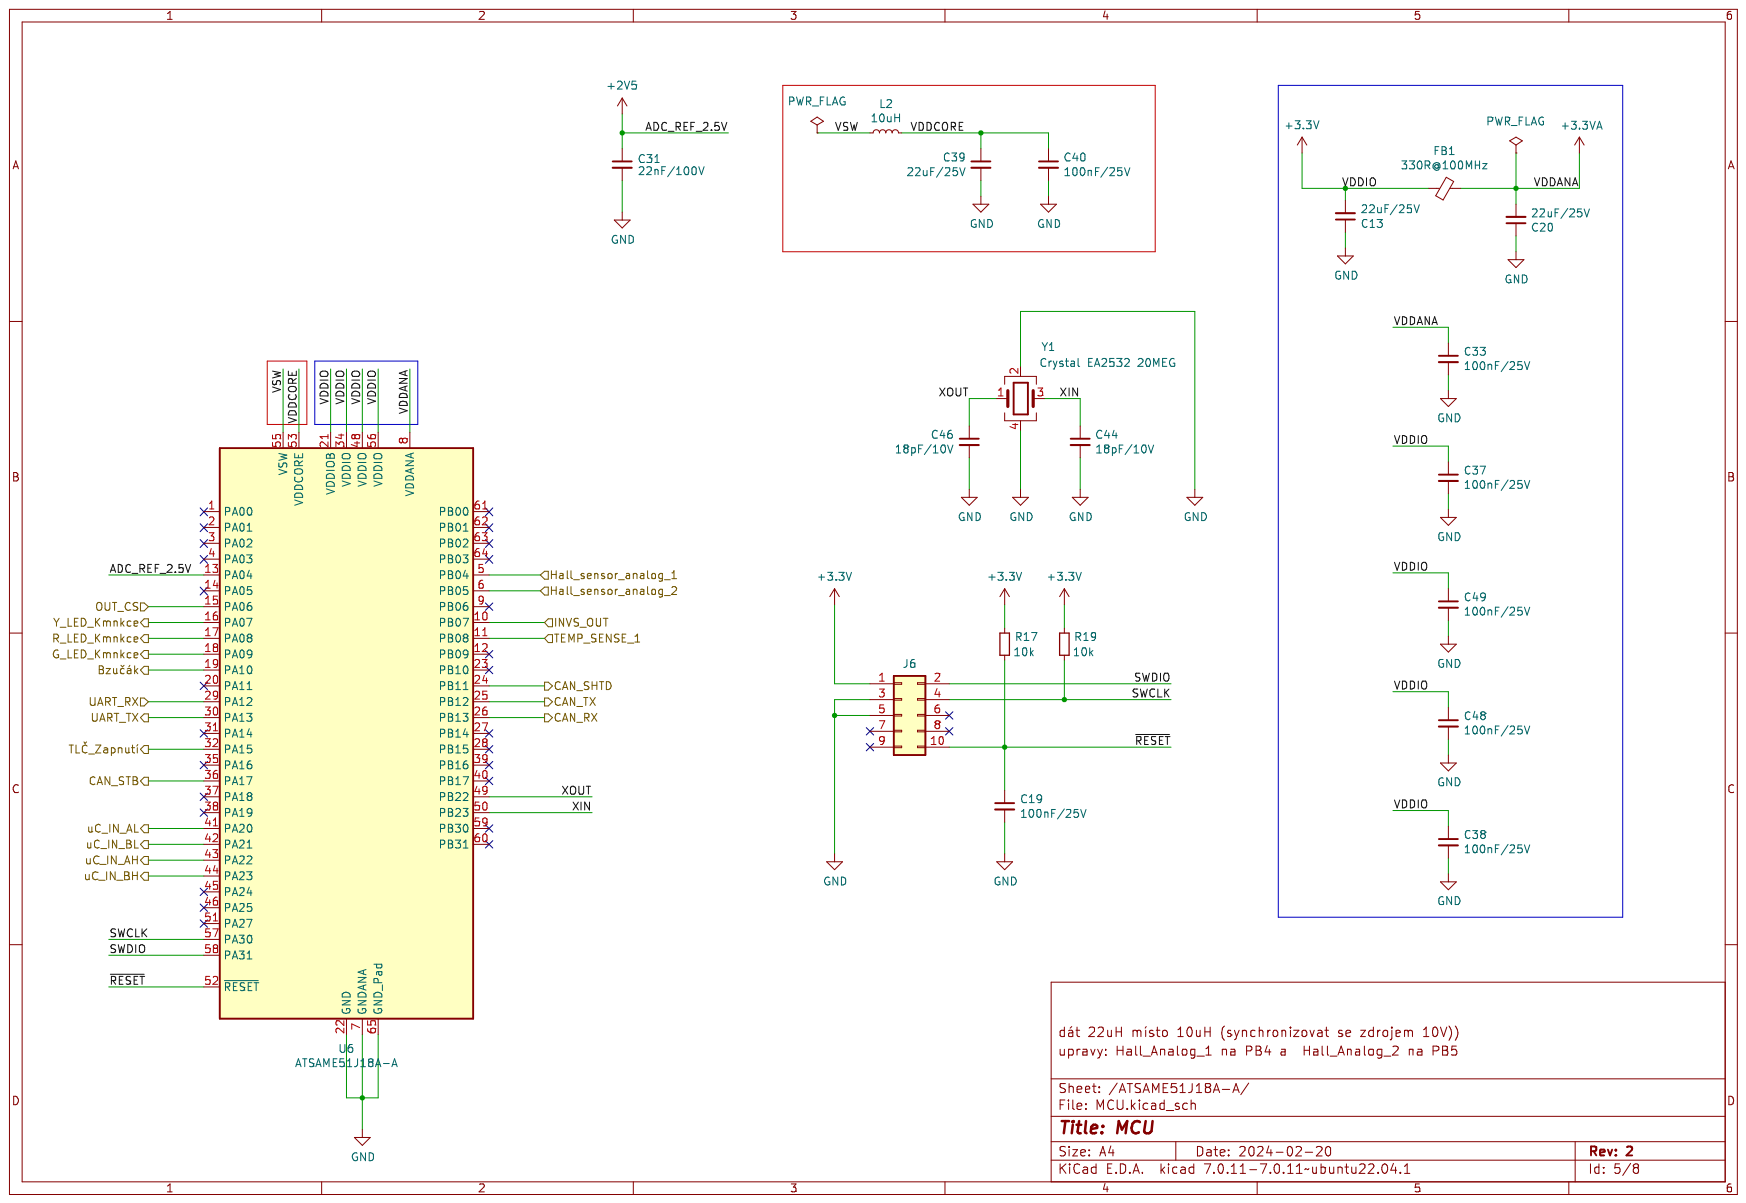
[picture p69: page 5]

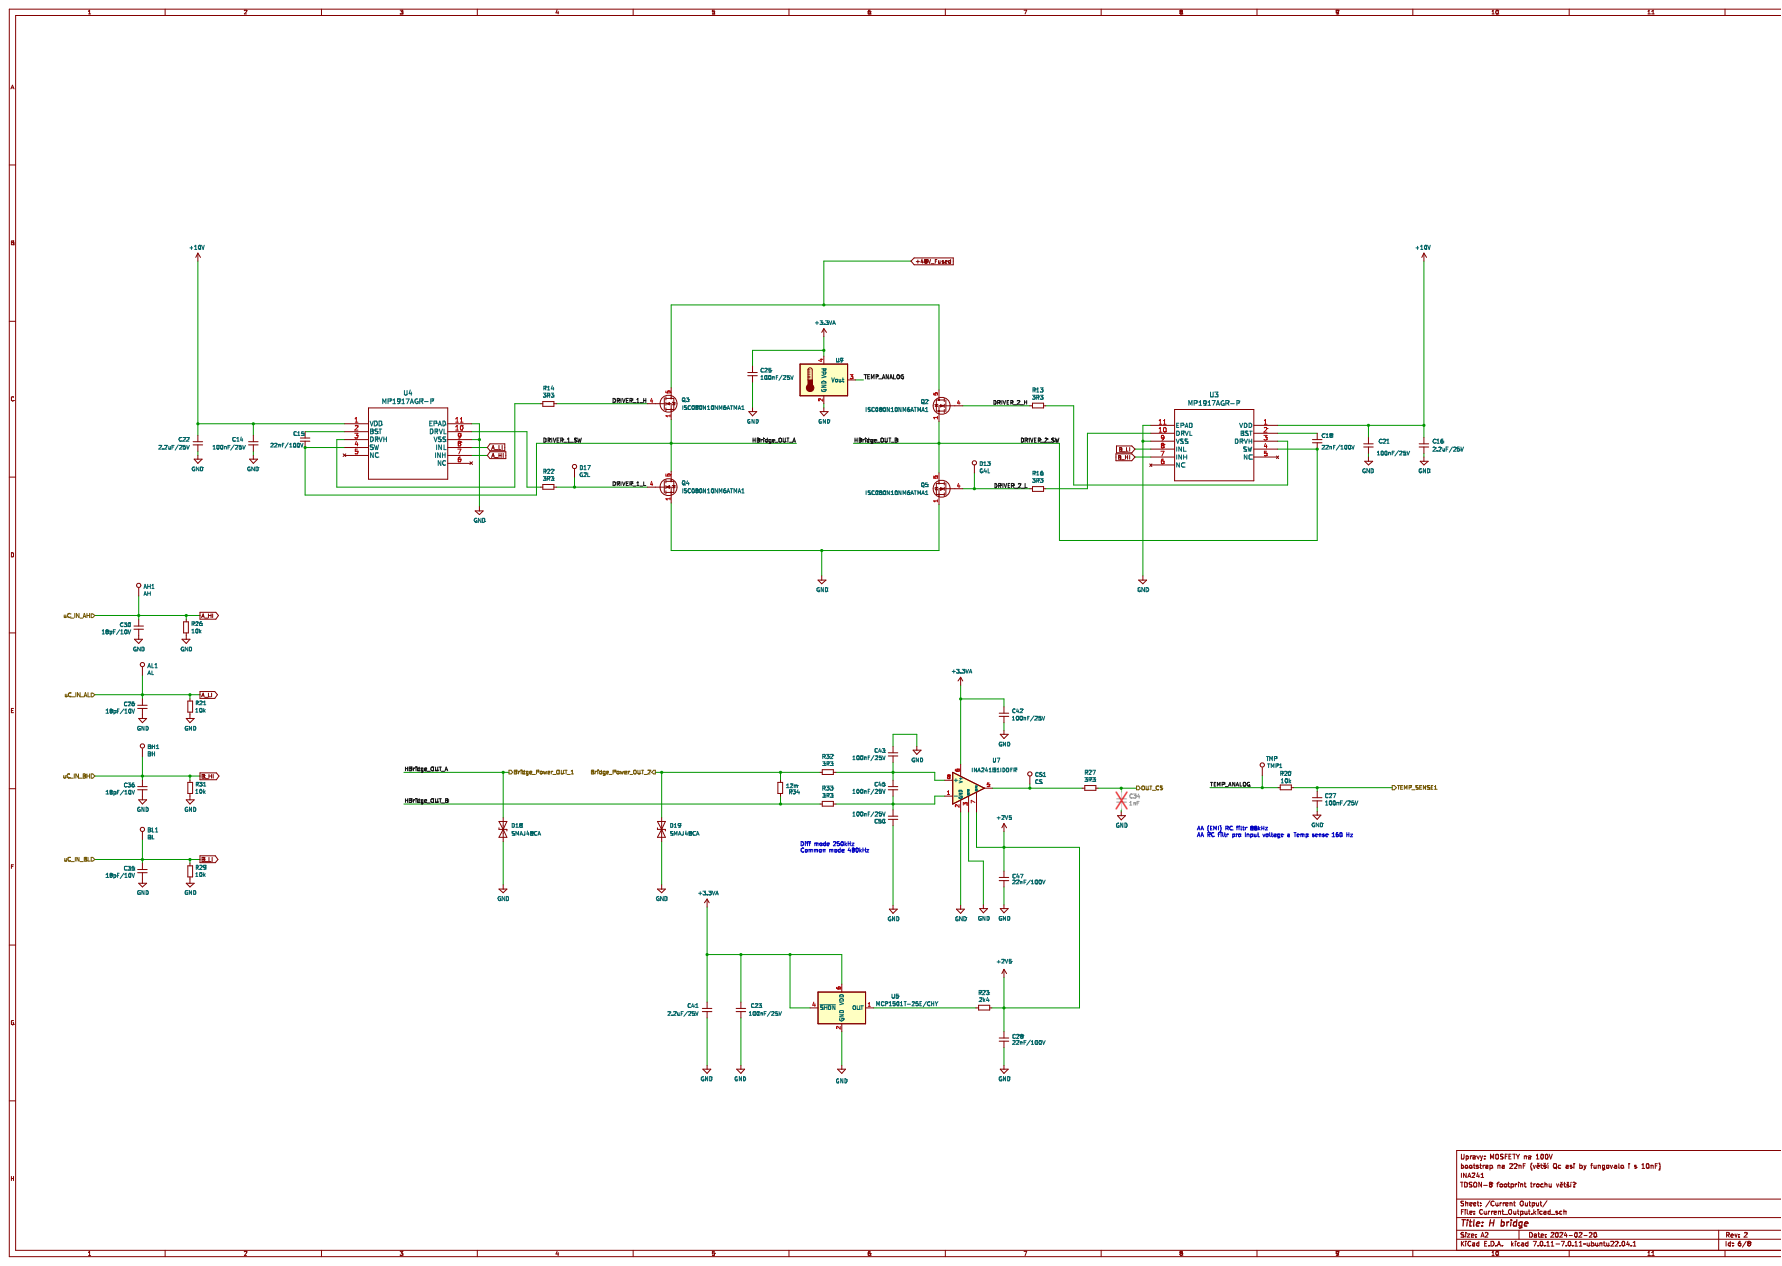
[picture p70: page 6]

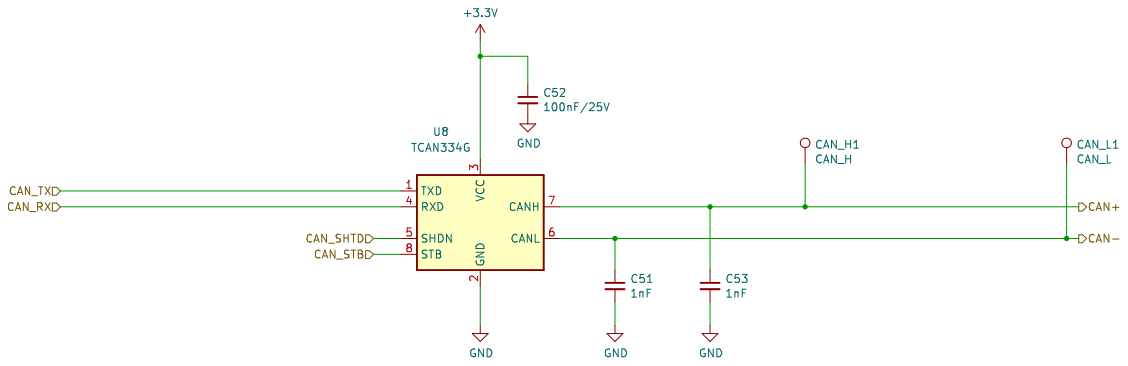
[picture p71: page 7]

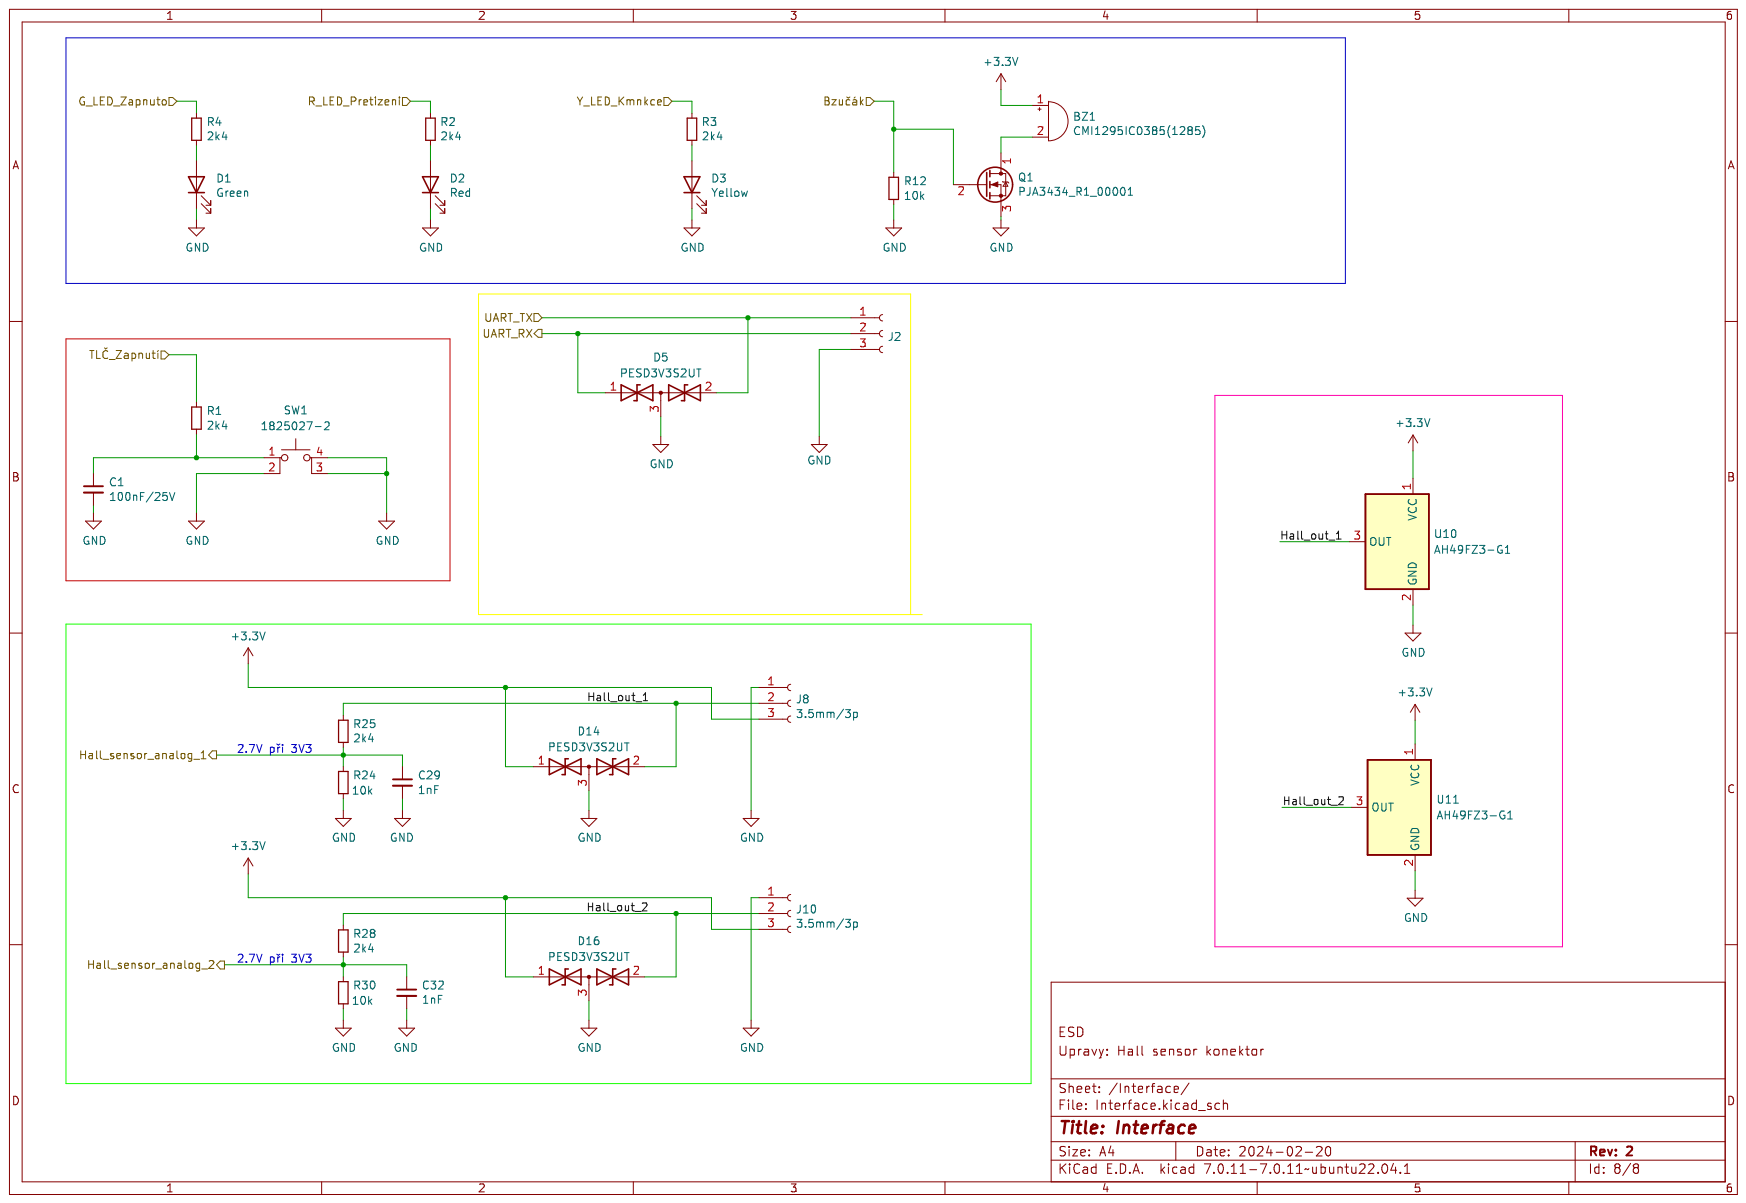
[picture p72: page 8]
