P4V77/DiplomaThesis/LaTeX/prilohy/prilohaC/emc_mozes.pdf

### ZČU – moses

### Datum měření: 4. 4. 2025

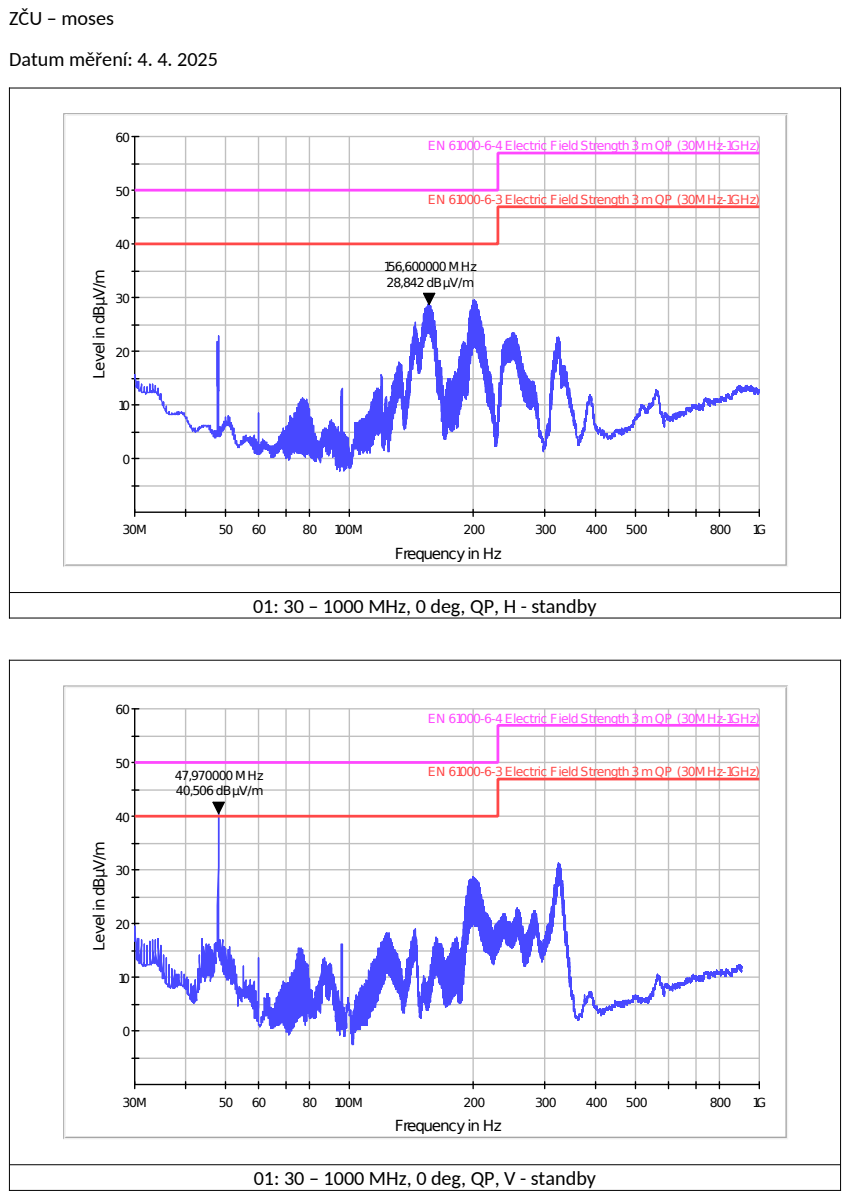
[picture p73: page 1]
47,970000 MHz 40,506 dBµV/m

EN 61000-6-4 Electric Field Strength 3 m QP (30MHz-1GHz)

EN 61000-6-3 Electric Field Strength 3 m QP (30MHz-1GHz)

156,600000 MHz
28,842 dBµV/m

Level in dBµV/m

Frequency in Hz

01: 30 – 1000 MHz, 0 deg, QP, H - standby

01: 30 – 1000 MHz, 0 deg, QP, V - standby

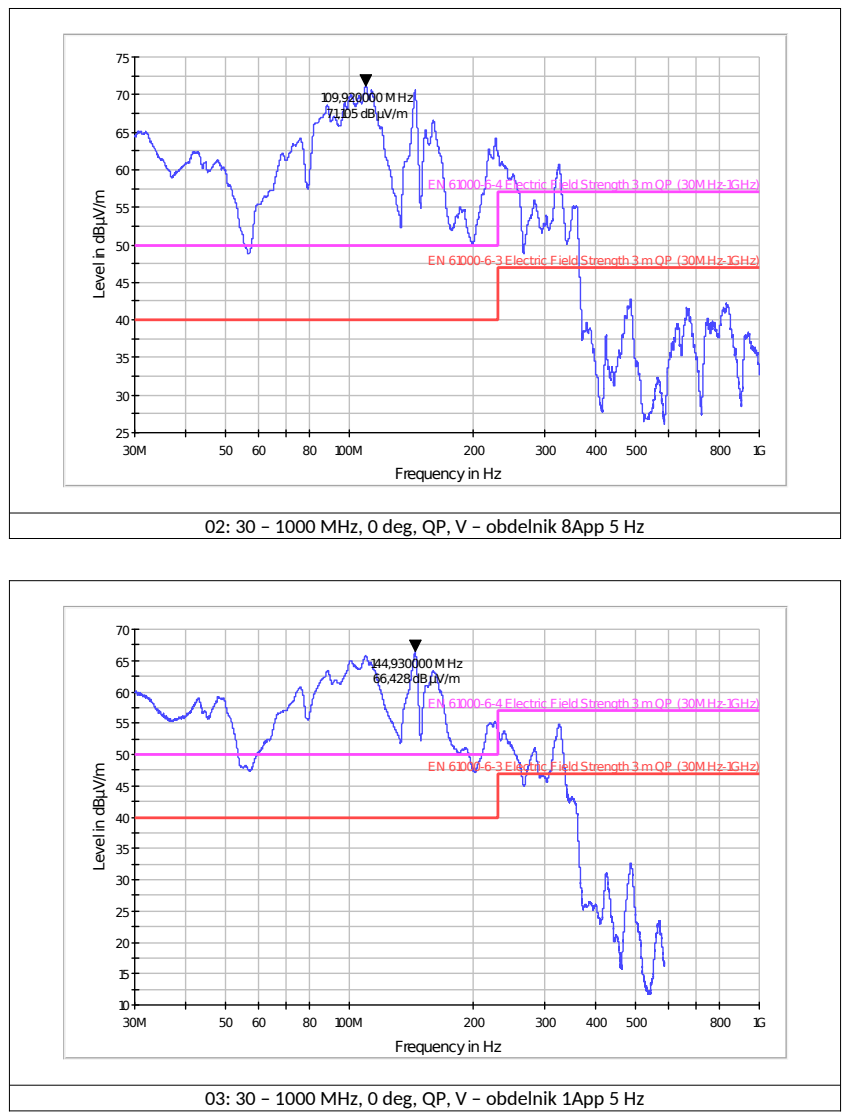
[picture p74: page 2]
109,920000 MHz 71,105 dBµV/m

Level in dBµV/m

EN 61000-6-4 Electric Field Strength 3 m QP (30MHz-1GHz)

EN 61000-6-3 Electric Field Strength 3 m QP (30MHz-1GHz)

Frequency in Hz

02: 30 – 1000 MHz, 0 deg, QP, V – obdelnik 8App 5 Hz

144,930000 MHz
66,428 dBµV/m

03: 30 – 1000 MHz, 0 deg, QP, V – obdelnik 1App 5 Hz

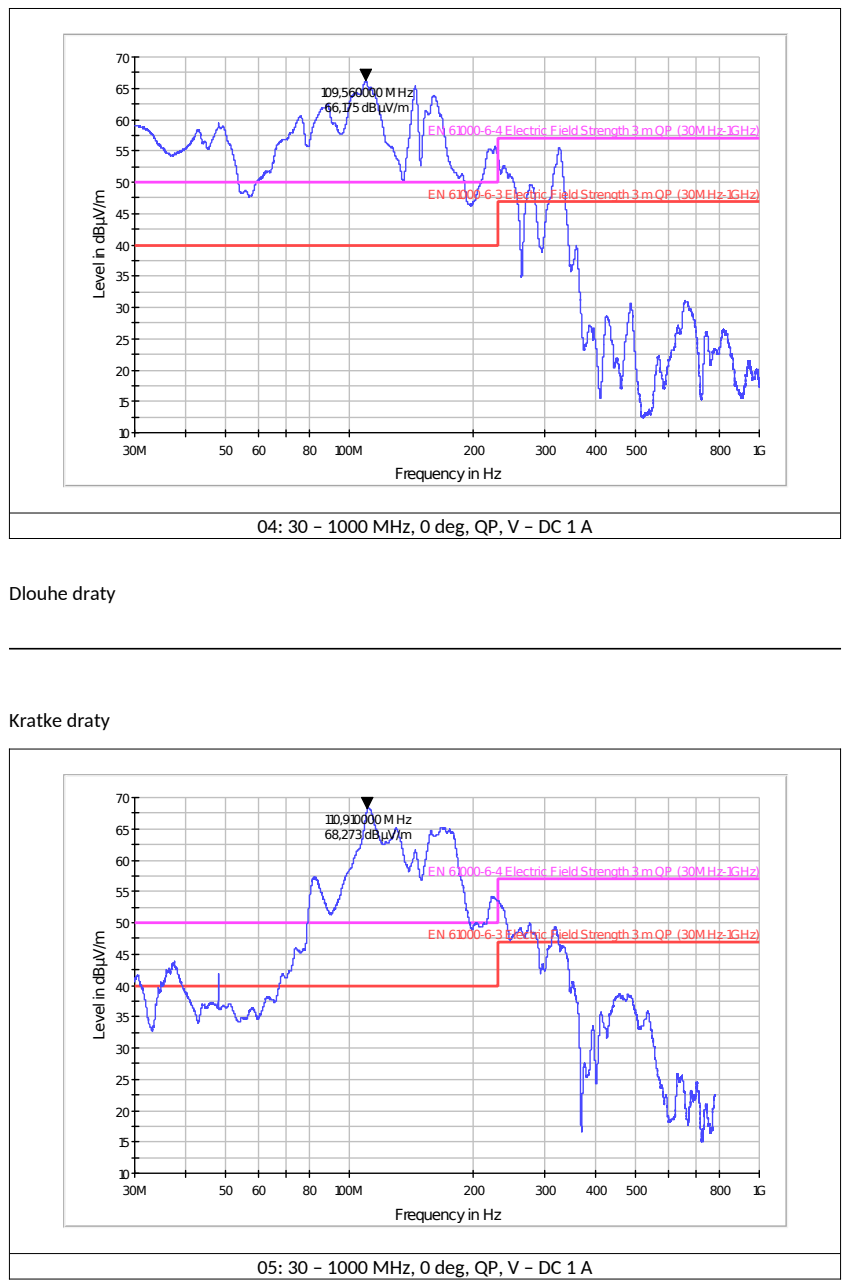
[picture p75: page 3]
Dlouhe draty; Kratke draty

109,560000 MHz
66,175 dBµV/m

EN 61000-6-4 Electric Field Strength 3 m QP (30MHz-1GHz)

Level in dBµV/m

EN 61000-6-3 Electric Field Strength 3 m QP (30MHz-1GHz)

Frequency in Hz

04: 30 – 1000 MHz, 0 deg, QP, V – DC 1 A

110,910000 MHz
68,273 dBµV/m

05: 30 – 1000 MHz, 0 deg, QP, V – DC 1 A

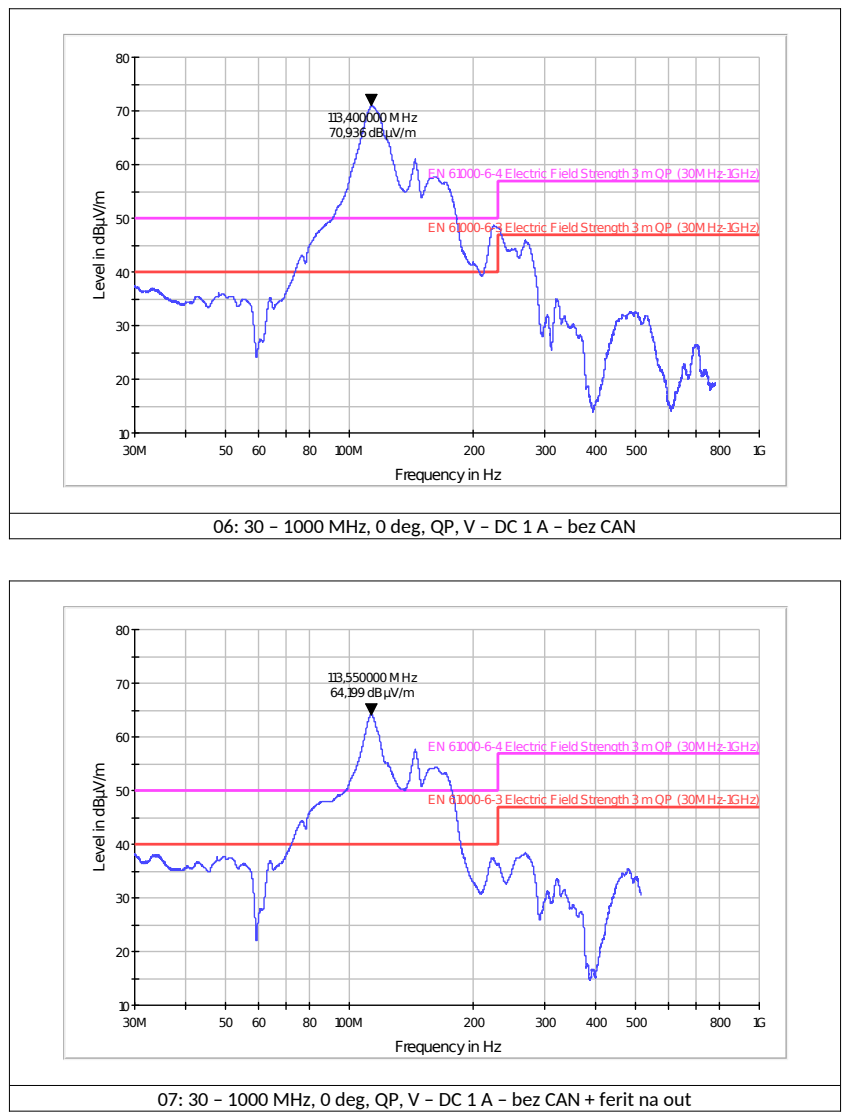
[picture p76: page 4]
113,400000 MHz 70,936 dBµV/m

EN 61000-6-4 Electric Field Strength 3 m QP (30MHz-1GHz)

Level in dBµV/m

EN 61000-6-3 Electric Field Strength 3 m QP (30MHz-1GHz)

Frequency in Hz

06: 30 – 1000 MHz, 0 deg, QP, V – DC 1 A – bez CAN

113,550000 MHz
64,199 dBµV/m

07: 30 – 1000 MHz, 0 deg, QP, V – DC 1 A – bez CAN + ferit na out

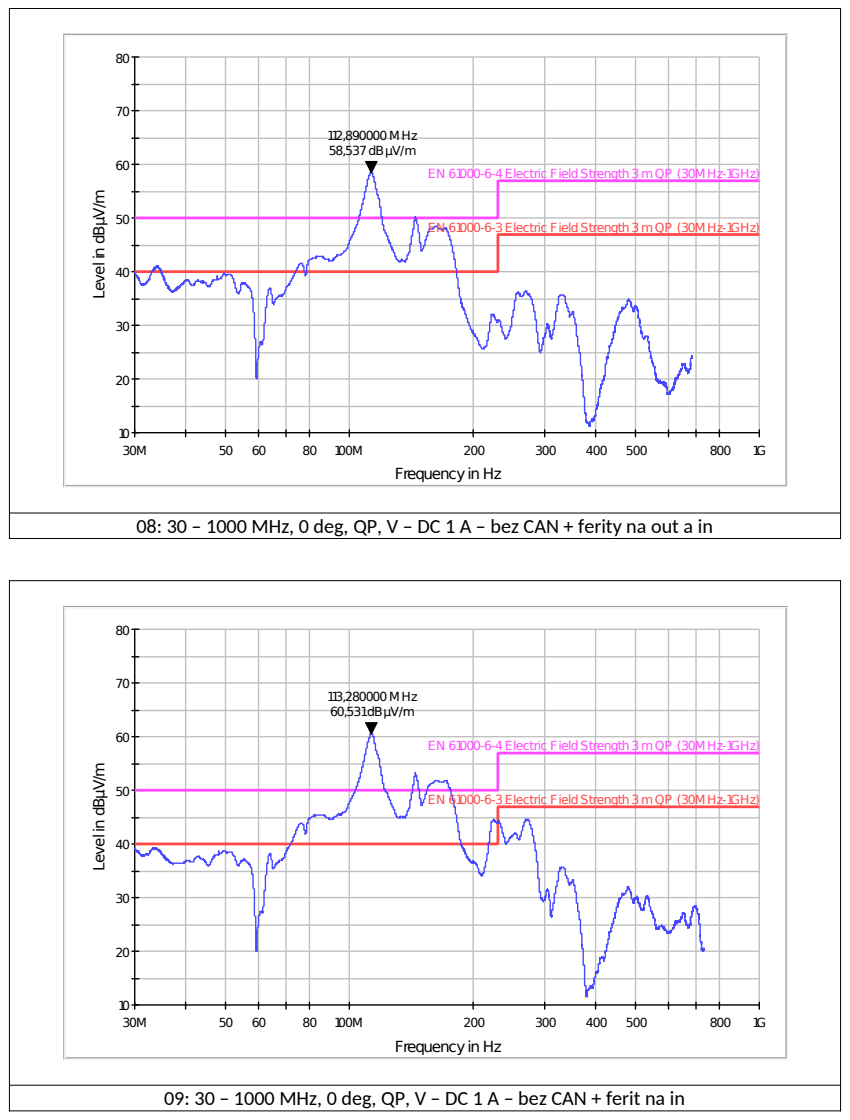
[picture p77: page 5]
113,280000 MHz 60,531 dBµV/m

112,890000 MHz
58,537 dBµV/m

EN 61000-6-4 Electric Field Strength 3 m QP (30MHz-1GHz)

Level in dBµV/m

EN 61000-6-3 Electric Field Strength 3 m QP (30MHz-1GHz)

Frequency in Hz

08: 30 – 1000 MHz, 0 deg, QP, V – DC 1 A – bez CAN + ferity na out a in

09: 30 – 1000 MHz, 0 deg, QP, V – DC 1 A – bez CAN + ferit na in

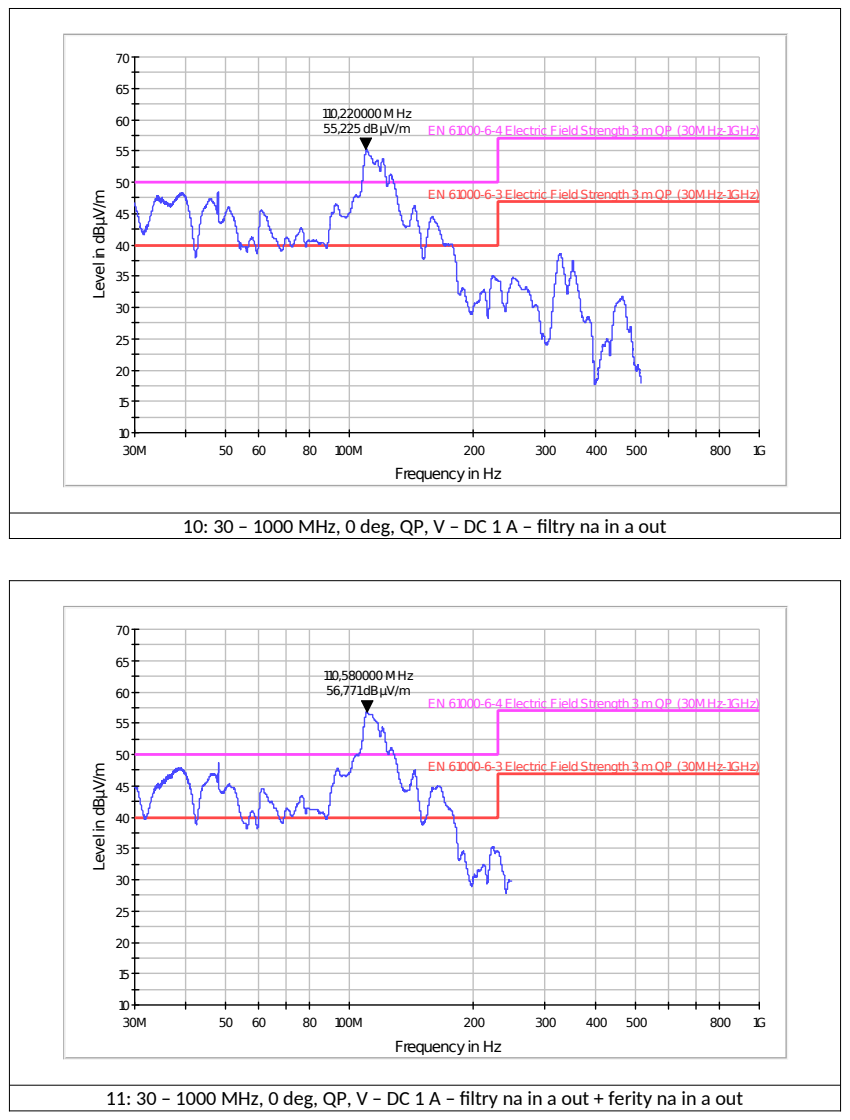
[picture p78: page 6]

110,220000 MHz
55,225 dBµV/m | EN 61000-6-4 Electric Field Strength 3 m QP (30MHz-1GHz)

Level in dBµV/m

EN 61000-6-3 Electric Field Strength 3 m QP (30MHz-1GHz)

Frequency in Hz

10: 30 – 1000 MHz, 0 deg, QP, V – DC 1 A – filtry na in a out

110,580000 MHz
56,771 dBµV/m

EN 61000-6-4 Electric Field Strength 3 m QP (30MHz-1GHz)

11: 30 – 1000 MHz, 0 deg, QP, V – DC 1 A – filtry na in a out + ferity na in a out

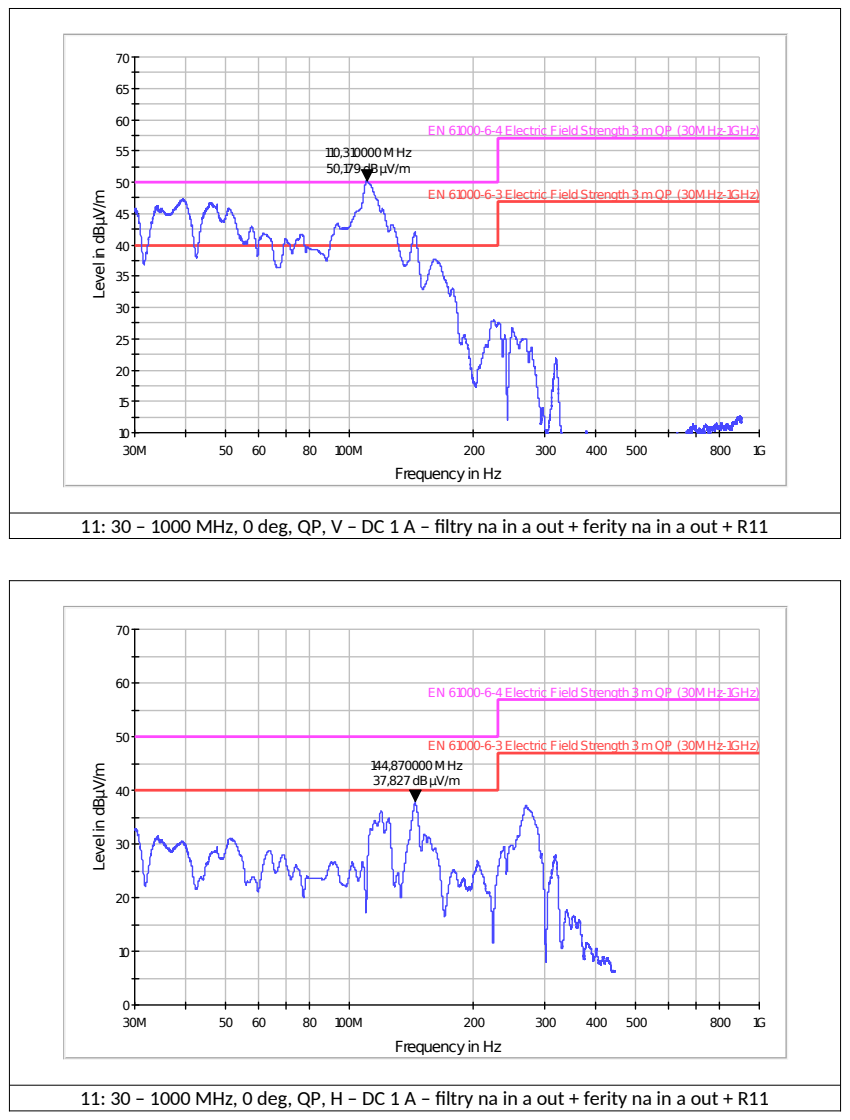
[picture p79: page 7]
110,310000 MHz 50,179 dBµV/m

EN 61000-6-4 Electric Field Strength 3 m QP (30MHz-1GHz)

Level in dBµV/m

EN 61000-6-3 Electric Field Strength 3 m QP (30MHz-1GHz)

Frequency in Hz

11: 30 – 1000 MHz, 0 deg, QP, V – DC 1 A – filtry na in a out + ferity na in a out + R11

144,870000 MHz 37,827 dBµV/m

11: 30 – 1000 MHz, 0 deg, QP, H – DC 1 A – filtry na in a out + ferity na in a out + R11
