P4V77/DiplomaThesis/FW/src/aron/h_interp.hpp

#ifndef H_INTERP_HPP
#define H_INTERP_HPP

namespace position_LUT
{

    constexpr float lut_voltage_min = 0.880737f;
    constexpr float lut_voltage_max = 1.440000f;
    constexpr float lut_voltage_resolution = 0.001119f;
    constexpr uint16_t lut_voltage_range = 499;
    const float LUT[] = {
        9.200000f,
        9.028929f,
        8.859959f,
        8.693078f,
        8.528277f,
        8.359160f,
        8.184349f,
        8.047826f,
        7.960136f,
        7.887612f,
        7.825966f,
        7.771131f,
        7.719039f,
        7.665624f,
        7.606817f,
        7.539245f,
        7.470177f,
        7.399884f,
        7.324757f,
        7.241186f,
        7.145563f,
        6.980890f,
        6.778211f,
        6.690086f,
        6.627026f,
        6.574758f,
        6.530341f,
        6.490838f,
        6.453311f,
        6.414821f,
        6.372429f,
        6.323197f,
        6.264667f,
        6.200127f,
        6.133481f,
        6.068030f,
        6.007074f,
        5.953221f,
        5.904281f,
        5.859052f,
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
    };
}

#endif // H_INTERP_HPP
